impatrq/AVIS/Compras/Plantilla de Compras Completo/Gasto Total de SKYLF.pdf

# Gasto Total de SKYLF

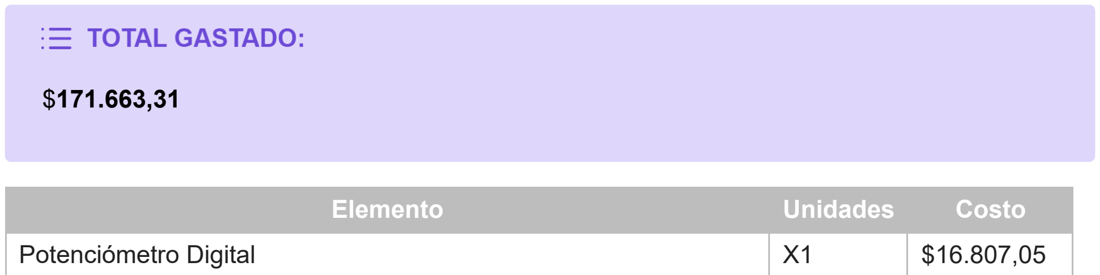
[picture p51: figure]
Elemento; Unidades; Costo; Potenciómetro Digital

Cables macho-macho | X1 | $4.900
MODULO ARDUINO CONVERSOR RS485 A TTL | X3 | $11.611,34
MODULO WIFI Y BLUETOOTH SERIE 32 BIT (30 PINES) | X1 | $23.795,07
ACELEROMETRO GIRÓSCOPO 6 EJES (MPU6050) | X1 | $3.090,90
PB20S HEMBRA 20 VIAS RECTO (Zócalos) | X2 | $1.435,06
PUL-ST030-N 15MM (Pulsadores) | X8 | $9.714,28
MECHA PARA METAL | X2 | $9.500
Disco de corte | X2 | $7.400
Tornillos | X17 | $1.700
Discos Flap | X2 | $10.400
Tuercas | X7 | $840
Arandelas | X10 | $1.100
Adaptador HDMI a VGA | X1 | $8.000
Optoacoplador | X8 | $11.200
Cables Macho-Macho 20cm Dupont | X40 | $4.500
Bulones | X11 | $3.550
Tuercas 1/4 | X6 | $320
Tuercas 1/2 | X3 | $600
1 Varilla Enroscada 100CM, 10 Tornillos, 10 Tuercas, 10 Arandelas | X1 | $4.000
WD-40 | X1 | $5.800
Disco Tyrolit Básico | X1 | $4.000
Cable HDMI | X1 | $6.500
Adaptador DisplayPort a HDMI | X1 | $9.500
Placa virgen 15cmx15cm | X1 | $4.100
Tornillos y Arandelas | X1 | $1.500
Llave Rotativa de 6 estados 1P6W | X1 | $3.260,37
TOTAL | | $169.124,07

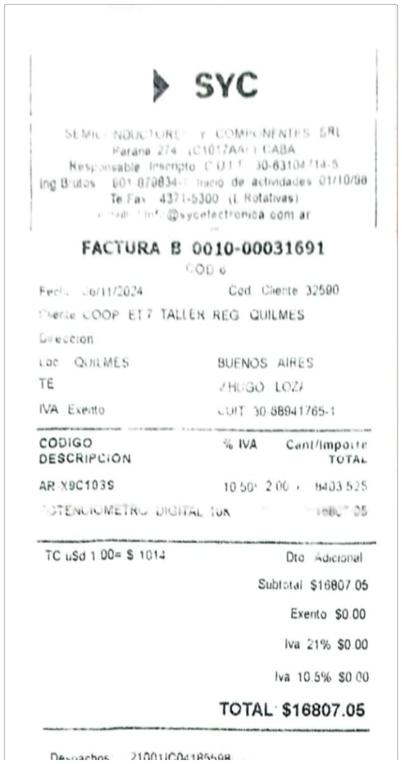
[picture p52: page 3]

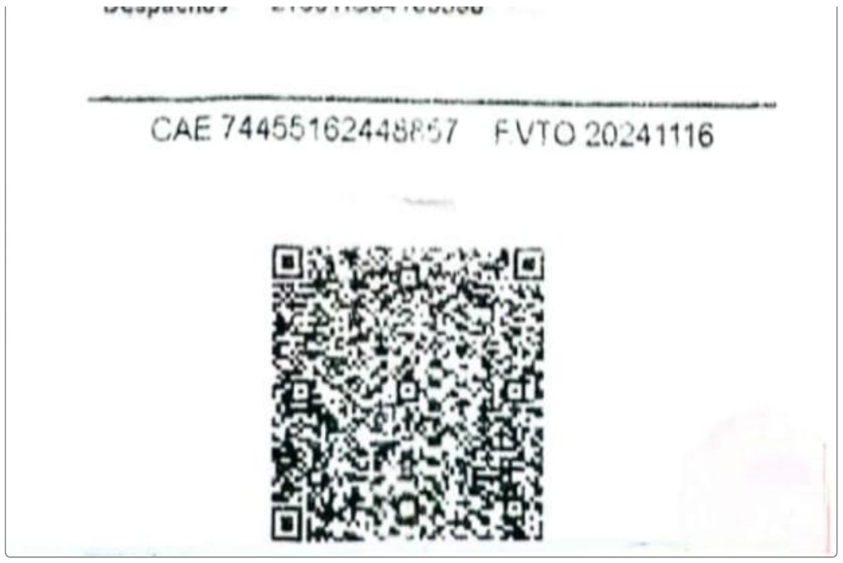
[picture p53: figure]
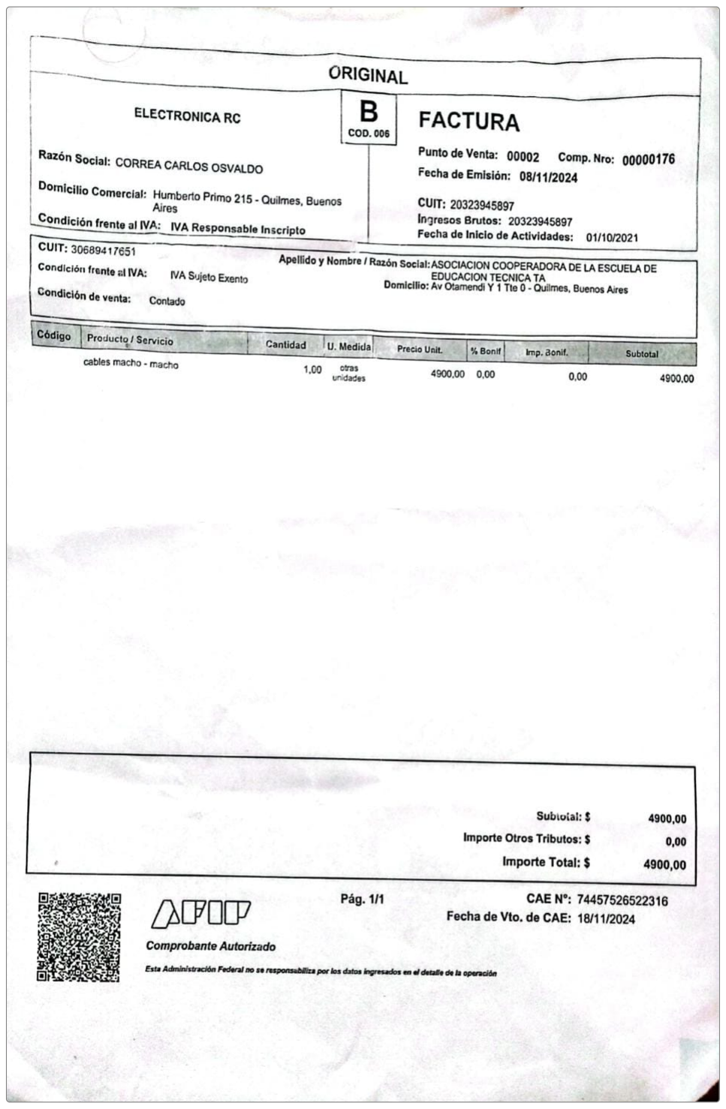
[picture p54: page 5]

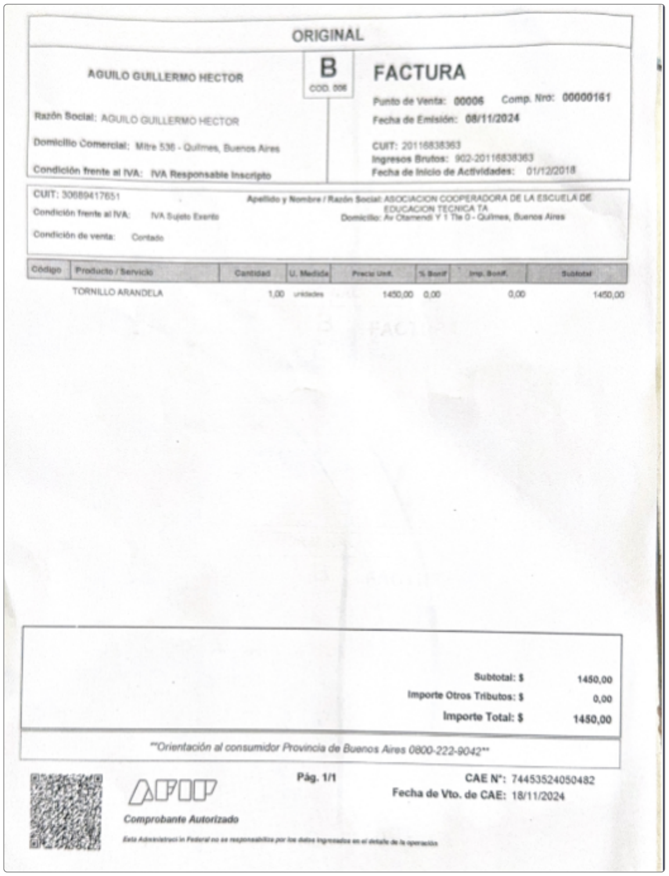
[picture p55: figure]
