impatrq/AVIS/Documentacion/Carpeta de campo y tecnica/Carpeta Técnica/Carpeta Tecnica SkylF .pdf

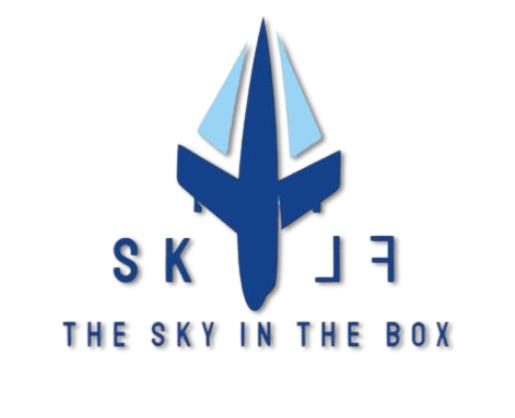
[picture p56: figure]

- Esteban Lautaro.
- Rubio Santiago Gabriel.
- Meabrio Lucas David.
- Flores Leandro.
- Brizuela Agustín.
- Leiva Santiago.
- Romocordoba Emiliano.
- Godoy Baldovino Jofiel

# S k y l F

# Integrantes

# Contacto

### Lautaro Esteban:

Mail: Lautyesteban14@gmail.com

Linkedin: Lautaro Sebastian Esteban (https://www.linkedin.com/in/lautaro-sebasti%C3%A1n-esteban-a5a8462a2)

Instagram: @lauty.esteban (https://www.instagram.com/lauty.esteban/profilecard/?igsh=MTU2dWFrOGU0dmdwdQ%3D%3D)

### Santiago Rubio:

Mail: Santy201205@gmail.com

Linkedin: Santiago Rubio (https://www.linkedin.com/in/santiago-rubio-a118932a8)

Instagram: @santy_201205 (https://www.instagram.com/santy_201205?igsh=MXU4d3c0bnNhZDNwZQ%3D%3D)

### Lucas Meabrio:

Mail: Meabriolucas@gmail.com

Linkedin: Lucas Meabrio (https://www.linkedin.com/in/lucas-meabrio-539666270/)

Instagram: @lucass_meab (https://www.instagram.com/lucass__meab?igsh=amc4NGF2cmF1d2J5)

### Leandro Flores:

Mail: leandro200flores@gmail.com

Linkedin: Leandro Flores (https://www.linkedin.com/in/leandro-flores-82538a2b0)

Instagram: @lean.floresss (https://www.instagram.com/lean.floresss?igsh=ZzdwNms0dDN3MDRu)

### Agustin Brizuela:

Mail: brizuu750@gmail.com

Linkedin: Agustin Lionel Brizuela (https://www.linkedin.com/in/agustin-lionel-brizuela-488690270)

Instagram: @agustiin.brizuela (https://www.instagram.com/agustiin.brizuela?igsh=MXFiYnRuNTdoem1uMg%3D%3D)

### Santiago Leiva:

Mail: Santiagoleiva745@gmail.com

Linkedin: Santiago Leiva (https://www.linkedin.com/in/santiago-leiva-3905942bb)

Instagram: @leivva.s (https://www.instagram.com/leivva.s?igsh=bDduN3BvdGFqMjRj)

### Emiliano Romocordoba:

Mail: Romoemiliano324@gmail.com

Linkedin:

Instagram:

### Jofiel Godoy Baldovino:

Mail: Markbaldj@gmail.com

Linkedin: Marco Baldovino (https://www.linkedin.com/in/marco-baldovino-b3948b2ba)

Instagram:@jofiel_godoy (https://www.instagram.com/jofiel_godoy?igsh=MXZpdGE5bm11NHJ5Nw%3D%3D)

# ÍNDICE

# Descripción del Proyecto:

# Variadores de Frecuencia:

Resumen del objetivo.

Lista de materiales usados.

# Paneles de Control:

# Descripción del Proyecto

Nuestro proyecto se enfocará en el armado y reacondicionamiento de un simulador de vuelo con el fin de recrear una experiencia inmersiva y entretenida para el que se meta dentro de la cabina.

# Variadores de Frecuencia

# Resumen del objetivo

El objetivo principal con el uso del variador de frecuencia es lograr una comunicación eficiente tanto con el programa de control como con los motores del simulador. Este tipo de comunicación es crucial para garantizar un funcionamiento sincronizado y preciso entre el software y el hardware. En nuestro caso, la comunicación se establece utilizando el protocolo Modbus, un estándar de comunicación ampliamente utilizado en sistemas industriales debido a su fiabilidad y flexibilidad.

El protocolo Modbus permite el intercambio de datos entre el variador de frecuencia y el microcontrolador ESP32, facilitando el control de parámetros clave como la velocidad y la dirección de los motores. Esta programación la estamos llevando a cabo mediante la plataforma Arduino IDE, donde se desarrollan los códigos que gestionan la interacción entre los distintos componentes del sistema. A través de Arduino IDE, se ha configurado el protocolo Modbus para que las señales enviadas desde el programa de simulación sean interpretadas correctamente por el variador de frecuencia, y a su vez, estas se traduzcan en comandos que controlan el movimiento de los motores.

# Lista de materiales usados

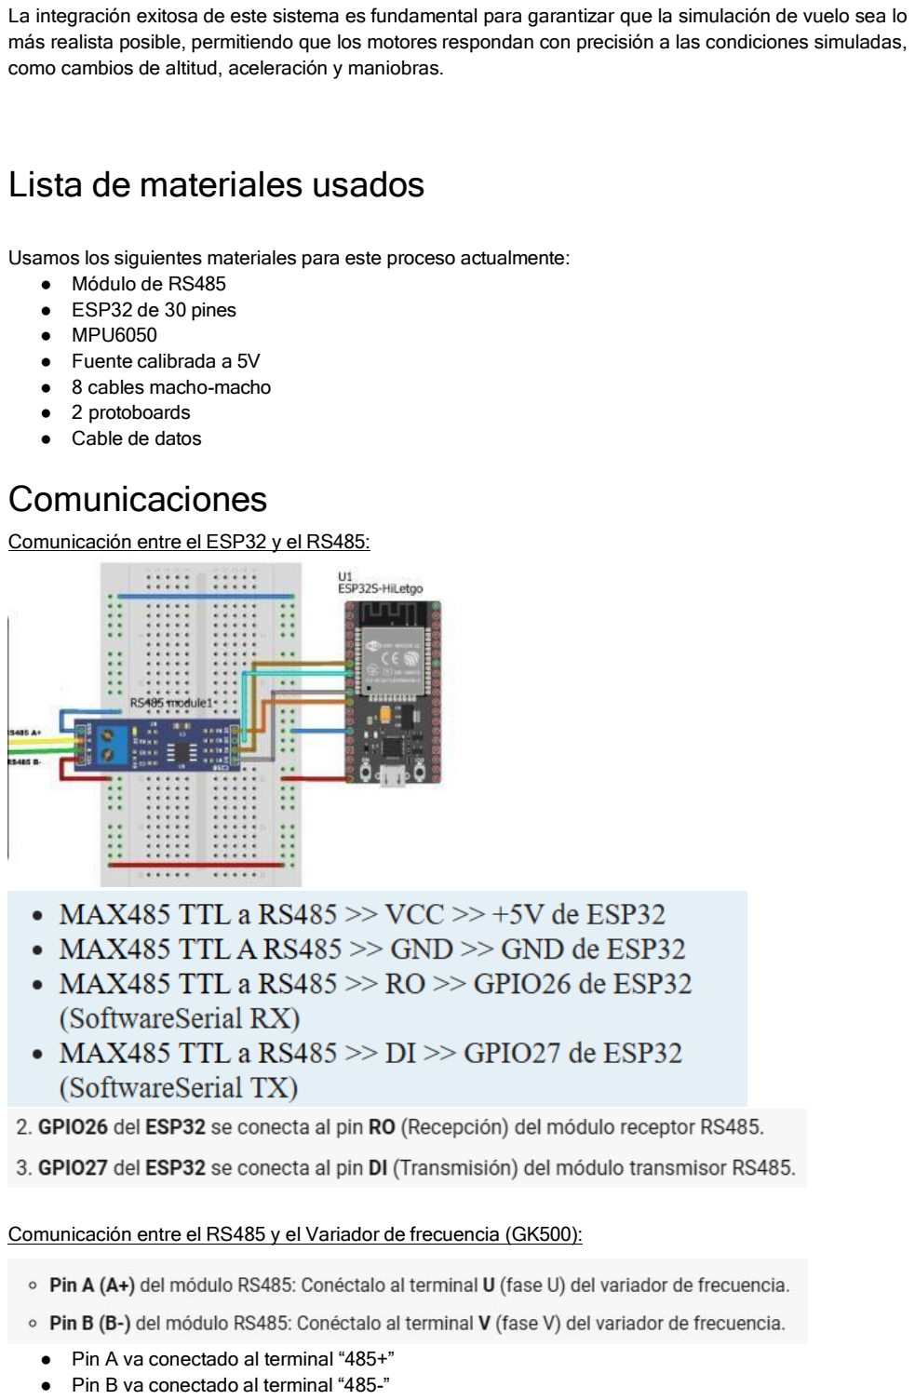
[picture p57: page 5]

La integración exitosa de este sistema es fundamental para garantizar que la simulación de vuelo sea lo más realista posible, permitiendo que los motores respondan con precisión a las condiciones simuladas, como cambios de altitud, aceleración y maniobras.

Usamos los siguientes materiales para este proceso actualmente:
- Módulo de RS485
- ESP32 de 30 pines
- MPU6050
- Fuente calibrada a 5V
- 8 cables macho-macho
- 2 protoboards
- Cable de datos

# Comunicaciones

Comunicación entre el ESP32 y el RS485:

Comunicación entre el RS485 y el Variador de frecuencia (GK500):

- Pin A va conectado al terminal “485+”
- Pin B va conectado al terminal “485-”

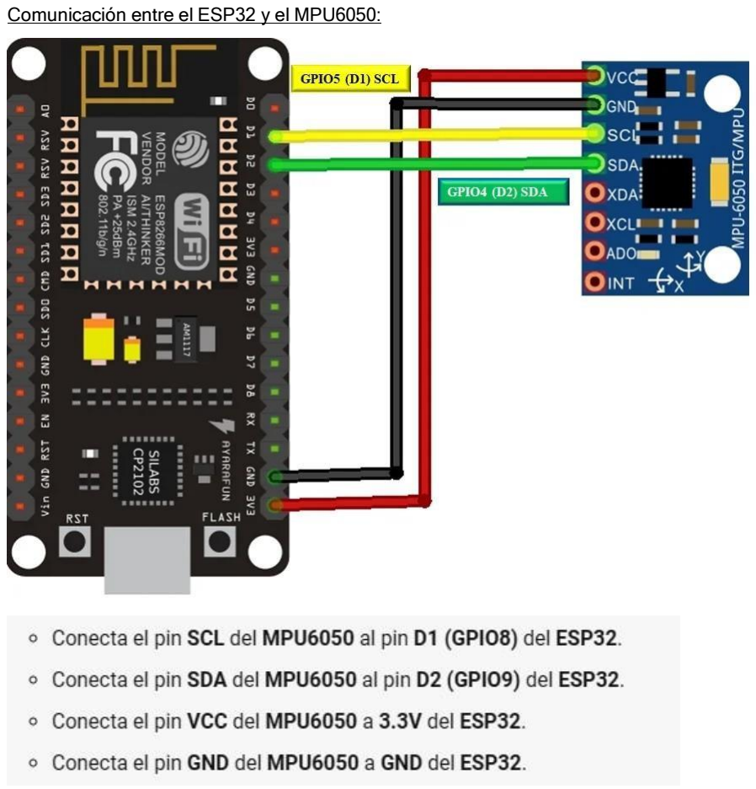
[picture p58: page 6]

Comunicación entre el ESP32 y el MPU6050:

# ESP32

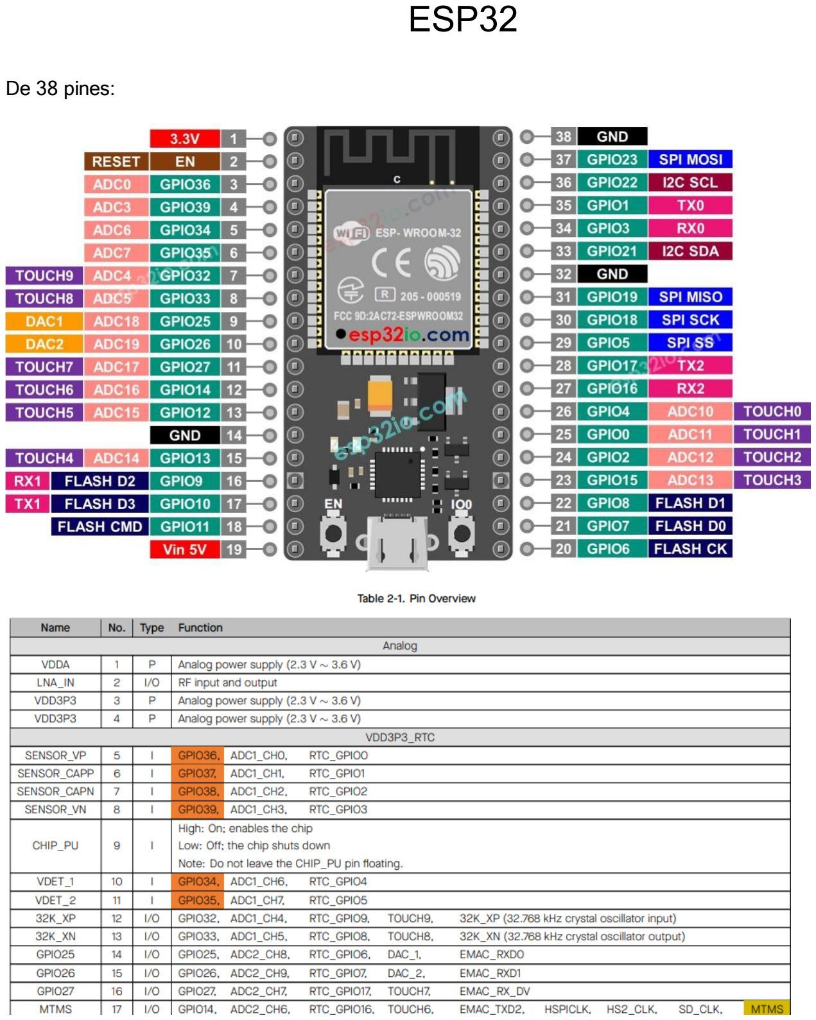
[picture p59: page 7]

De 38 pines:

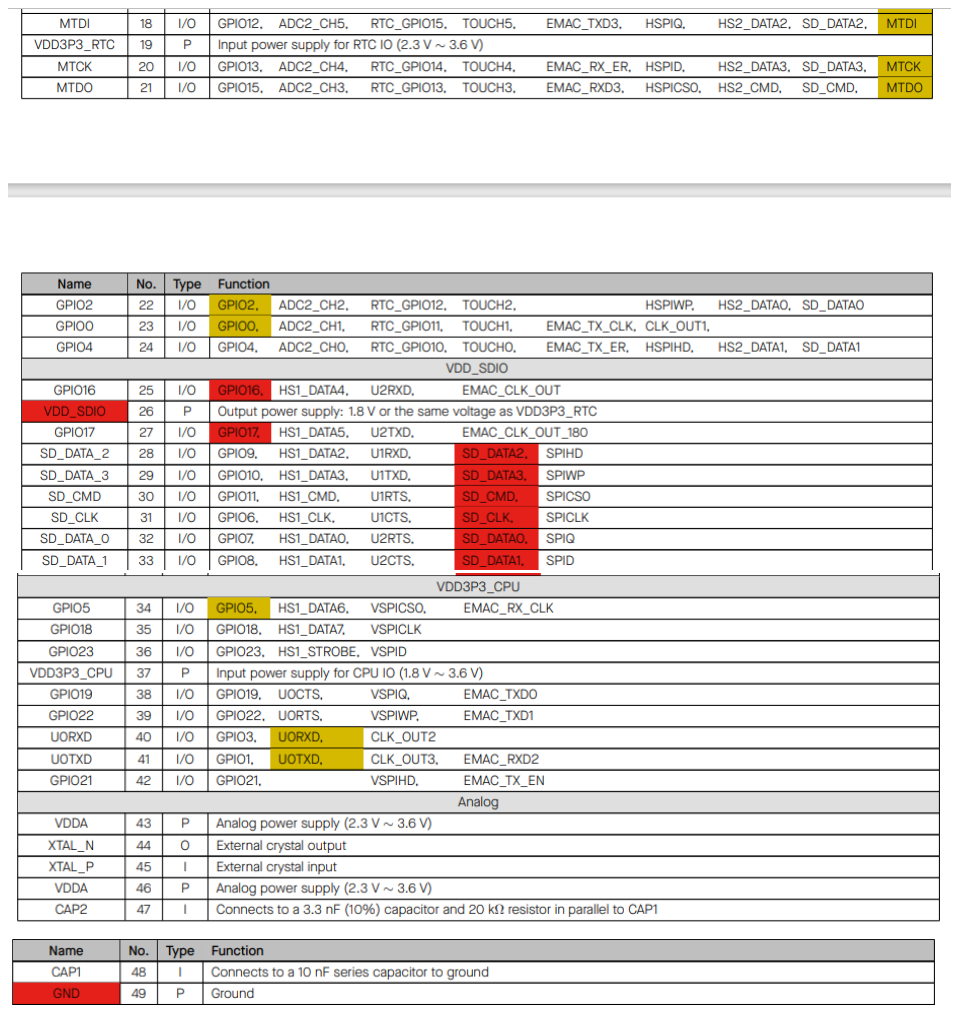
[picture p60: page 8]
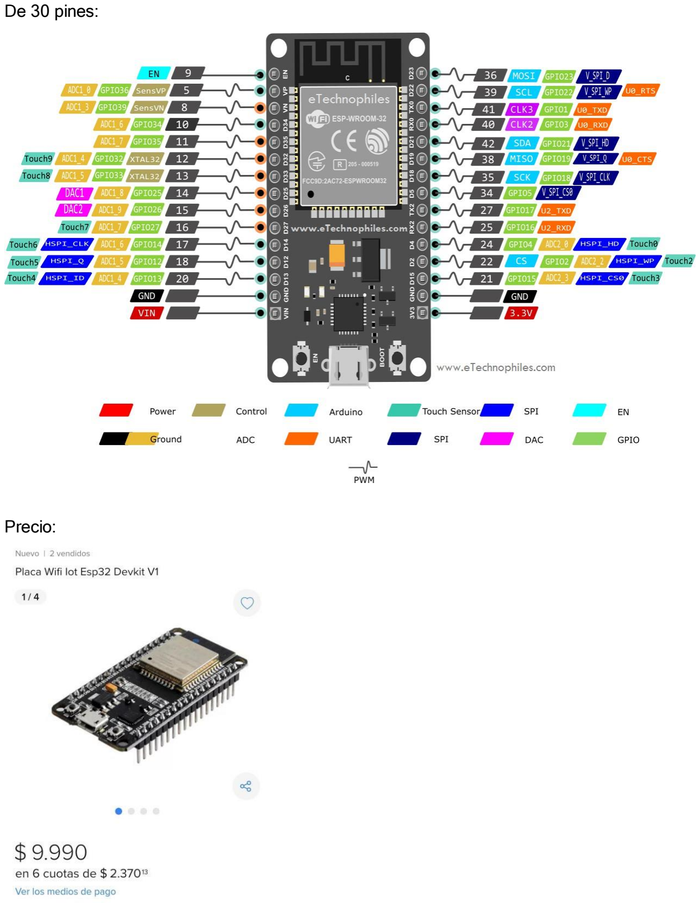
[picture p61: page 9]

De 30 pines:

Precio:

RS485

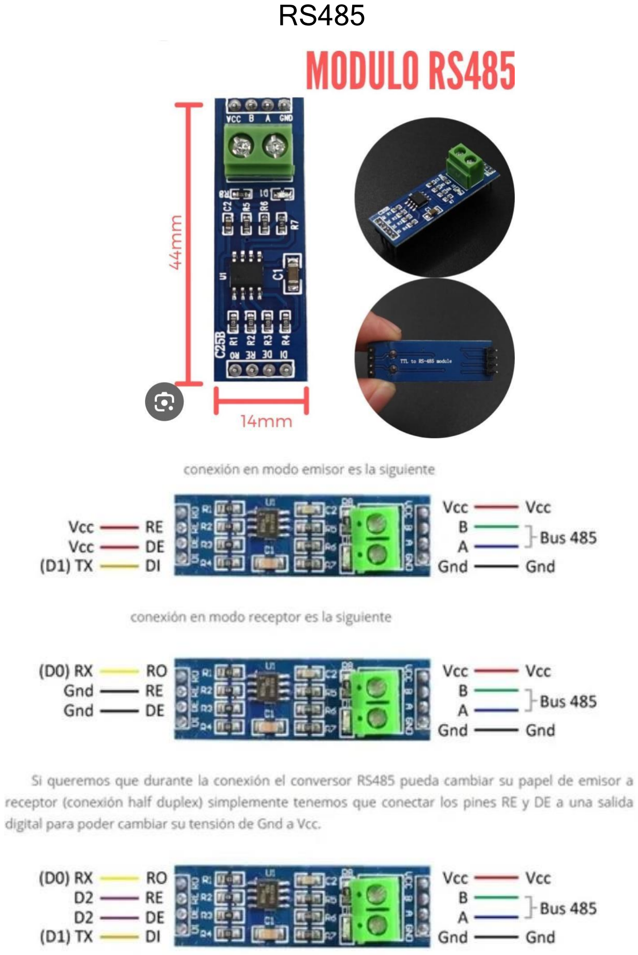
[picture p62: page 10]

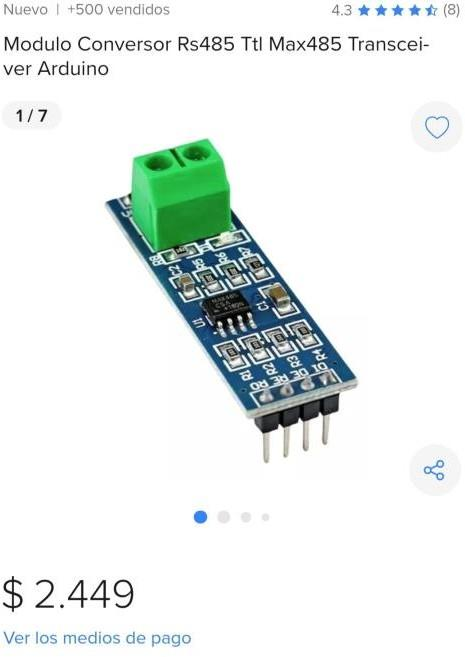
[picture p63: figure]

# MPU6050

El MPU6050 es una unidad de medición inercial o IMU (Inertial Measurment Units) de 6 grados de libertad, pues combina un acelerómetro de 3 ejes y un giroscopio de 3 ejes. Este sensor es muy utilizado en navegación, geometría, estabilización, etc. Este componente nos sirve para inclinar la cabina en sus 3 ejes, basándose en las mediciones de los SimVars.

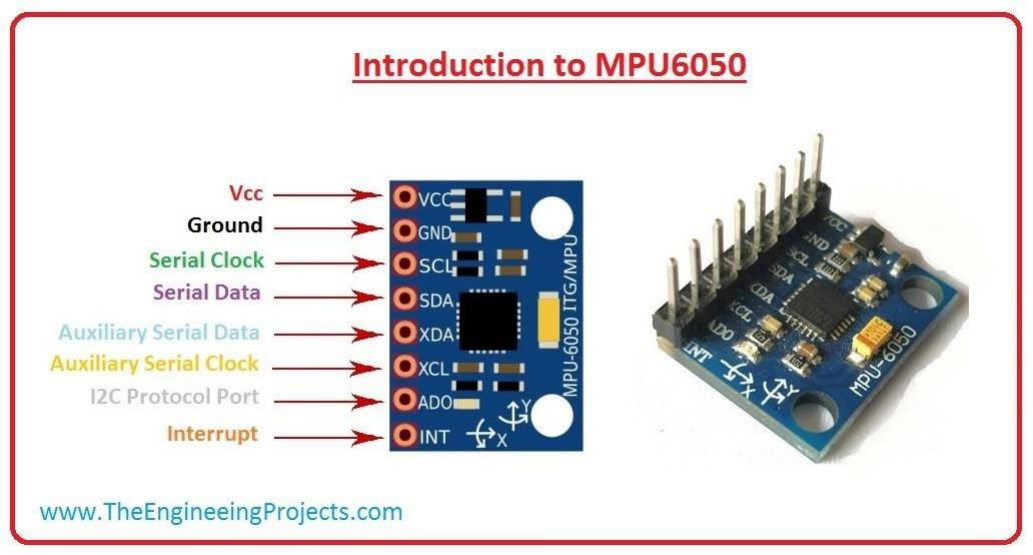
[picture p64: figure]

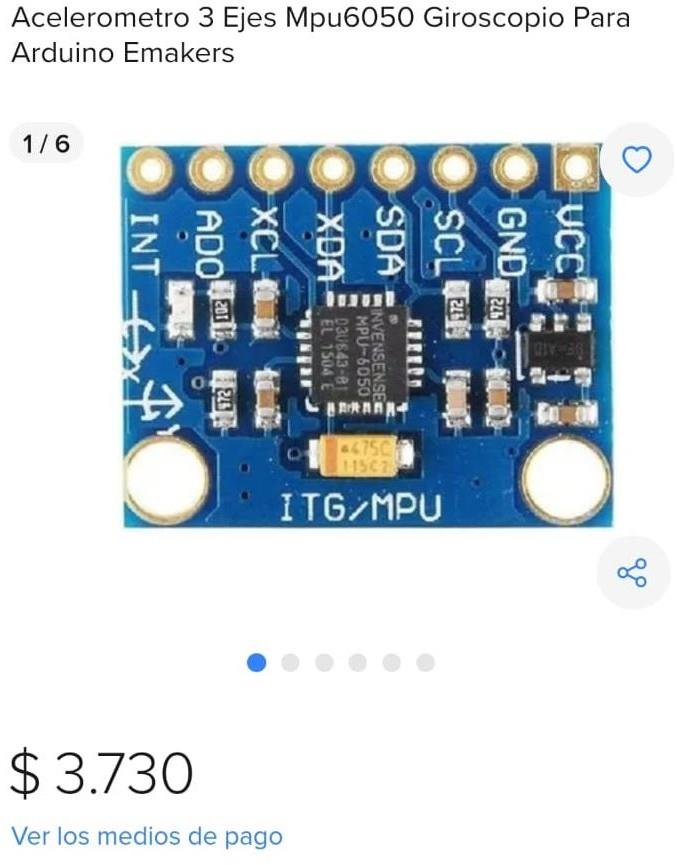
[picture p65: figure]

# Listado de parámetros que pusieron en el variador

Parámetros | Designación | Rango | Rango puesto
b0-01 | Fuente de Mando de Frecuencia Maestra | 0: Configuración Digital (b0-02) + ∧ /∨ Ajuste en Panel de Control 1: Configuración Digital (b0-02) + Ajuste por Bornera UP/DOWN 2: Entrada Analógica AI 3: Potenciómetro 6: Salida de PID 8: Comando Multivelocidad 9: Comunicación

9

9: Comunicación

b0-02 | Configuración Digital de Frecuencia Maestra | Límite Inferior ~ Límite Superior de Frecuencia

50,00 Hz

b1-00 | Comando RUN | 0: Control por Panel de Control 1: Control por Bornera 2: Control por Comunicación

2

2: Control por Comunicación

b1-01 | Enlace de comando run y configuración frecuencia | Unidades: Fuente de configuración frecuencia agrupada bajo control panel de control: 0: Sin enlace 1: Configuración Digital (b0-02) + ∧ /∨ Ajuste en Panel de Control 2: Configuración Digital (b0-02) + Ajuste por Bornera UP/DOWN 3: AI 4: Potenciómetro 7: Salida de PID 9: Comando Multivelocidad A: Entrada de Comunicación Decenas: Fuente de

AAA

A: Entrada de Comunicación

Parámetros | Designación | Rango | Rango puesto
| | configuración frecuencia agrupada bajo control terminal (igual a unidades) Centenas: Fuente de configuración frecuencia agrupada bajo control de comunicación (igual a unidades)
H0-01 | Configuración del Puerto de Comunicación RS-485 | Unidades: Velocidad en Baudios 0: 4800 bps 1: 9600 bps 2: 19200 bps 3: 38400 bps 4: 57600 bps Decenas: Formato de datos 0: Formato 1-8-2-N, RTU 1: Formato 1-8-1-E, RTU 2: Formato 1-8-1-O, RTU 3: Formato 1-7-2-N, ASCII 4: Formato 1-7-1-E, ASCII 5: Formato 1-7-1-O, ASCII Centenas: Tipo de conexión 0: Conexión cable directo (232/485) 1: MODEM (232) Unidades de Mil: Almacenamiento 0: Sin almacenar ante Pérdida de Energía 1: Almacenado ante Pérdida de Energía

0001

1: 9600bps

H0-05 | Opción Maestro/Esclavo

0: Se usa independientemente 1: Como Maestro
2: Como Esclavo

2

2: Como Esclavo

# Paneles de Control

El simulador posee dos paneles que cumplen su respectiva función; el panel de control (mediante palancas y botones interactuando con el entorno virtual) y el panel de instrumentos (estos se van a mostrar mediante una tele que transmite los datos reales de vuelo en los instrumentos)
El panel de control cuenta con todo el Hardware que se comunicará con el software a utilizar, (que en nuestro caso sería el Flight Simulator 2020).

## Panel de Control

En el panel de control hay 7 interruptores de palanca, una llave selectora rotativa de 6 estados y una llave con dos interruptores.
Para que estos componentes se accionen en simultáneo al vuelo que se haga en el Flight Simulator 2020, a través de una herramienta llamada "MobiFlight" y un Arduino UNO. Con el MobiFlight asignamos a cada componente a que realice determinada acción dentro del FS2020. Y con la Arduino UNO, en conjunto al MobiFlight, ejecuta esa acción a realizar
A continuación, explicaremos cuáles son estos componentes a utilizar y cuál es su función dentro del entorno virtual del FS2020:

Interruptores de palanca:

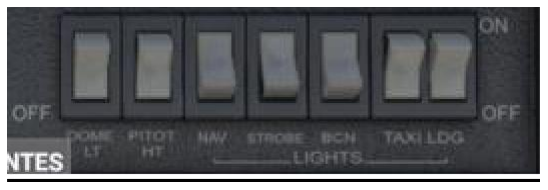
[picture p66: figure]

- 7 teclas de navegación:
- Tecla 1 “Dóme LT”: Cóntróla las luces interióres del avió´n.Se usa para iluminar la cabina durante el vueló nócturnó ó en cóndiciónes de póca luz.
- Tecla 2 “Pitót Hit”: Activa el sistema de calefacció´n del tubó Pitót.
- Tecla 3 “Nav”: Enciende las luces de navegació´n, que són las luces de pósició´n en las alas y la cóla.
- Tecla 4 “Stróbe”: Activa las luces estróbóscó´ picas, són luces blancas intermitentes en las alas.
- Tecla 5 “BCN”: Enciende la Luz de baliza (beacón), una luz rója intermitente ubicada en la parte superiór ó inferiór del fuselaje. Si el mótór este encendidó, esta luz siempre se encendera´.

- Tecla 6 “Taxi”: Enciende la luz de taxi, es una luz delantera usada para iluminar la pista mientras el avió´ n rueda pór el sueló.
- Tecla 7 “LDG”: Cóntróla la luz de aterrizaje, usada para iluminar la pista durante el aterrizaje ó despegue.
- Primer: se encarga de inyectar cómbustible a lós cilindrós del mótór antes de arrancarló, facilitandó el arranque en cóndiciónes especialmente frias. (Generalmente se bómbea 2 a 3 veces).
- Llaves:
- Llave maestra ALT: esta se encarga de encender el alternadór del mótór para póder cargar la baterí´a de la aerónave.
- Llave maestra Bat On/Off: esta se encarga de prender la baterí´a para que pueda alimentar lós circuitós ele´ctricós de la aerónave.

Magneto (con llave selectora rotativa de 6 estados):

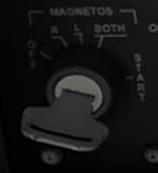
[picture p67: figure]

- Magnetó: este cuenta cón 5 estadós:
- Estadó 1 “OFF”: Ambós magnetós esta´n apagadós, y el mótór nó recibira´ chispa.
- Estadó 2 “Right”:Sóló el magnetó derechó estara´ encendidó.
- Estadó 3 “Left”:Sóló el magnetó Izquierdó estara´ encendidó.
- Estadó 4 “Bóth”: Ambós magnetós esta´n activós (pósició´n nórmal durante el vueló)
- Estadó 5 “Start”: Esta pósició´n activa el mótór de arranque y ambós magnetós, usada sóló para el encendidó del mótór

## Instrucciones de Configuración

Vinculación del MobiFlight con el FS2020 y el Arduino UNO

Para que el MobiFlight se vincule con el hardware del simulador de vuelo, nos tiene que aparecer en la barra inferior una tilde que confirme si se vincularon los siguientes parámetros:

Module:
- Si no hay ningún microcontrolador conectado al MobiFlight aparecerá un triangulo amarillo indicando eso

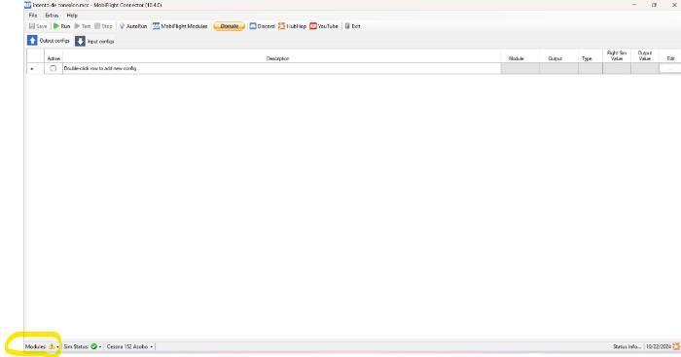
[picture p68: figure]

- Caso contrario, si está conectado al MobiFlight algún Microprocesador, (siendo el Arduino UNO en nuestro caso) se indicará que MobiFlight lo detectó correctamente.

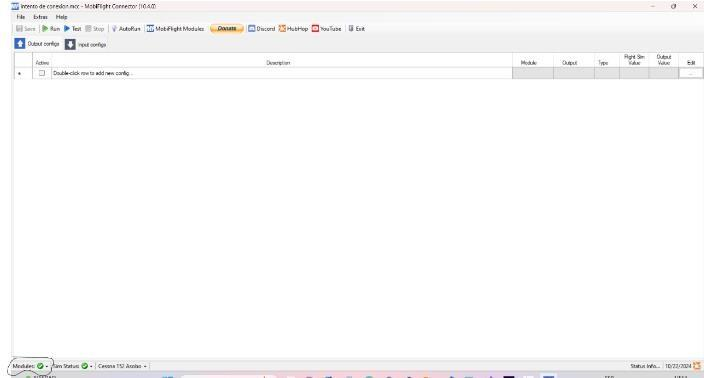
[picture p69: figure]

Sim Status
- El Sim Status indica el estado de las conexiones al simulador de vuelo
En nuestro caso usamos el programa "FSUIPC7" para que el FS2020 detecte el hardware. Así nos tiene que aparecer:

Configuración de las Palancas en el MobiFlight

Paso a Paso de configuración de palancas para vincularlas con MobiFlight y el FS2020

### 1. Conectamos elArduino UNOal MobiFlight y elFSUIPC7

### 2. Asignamos unPindel2 al13 delArduinoUNOa uno de los terminales de la palanca (En nuestro caso lo pusimos al pin 8 pero puede ser cualquiera)

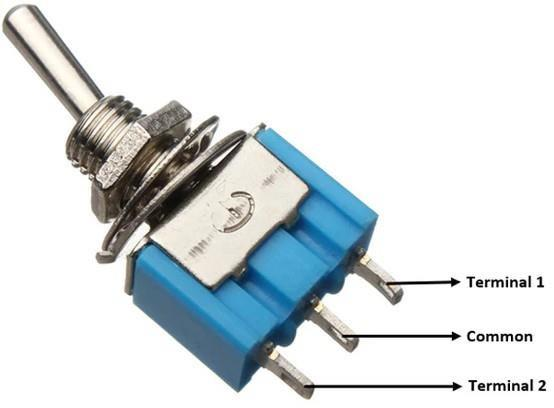
[picture p70: figure]

### 3. Seleccionar enMobiFlightla pestaña de "MobiFlight Modules"

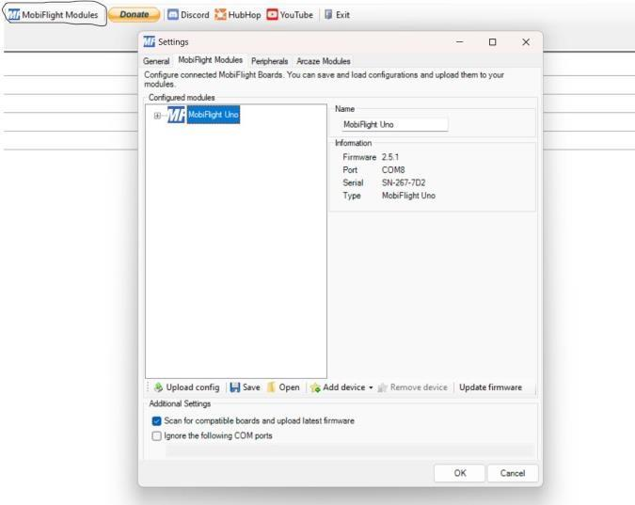
[picture p71: figure]

### 4. Para no tener inconvenientes actualizar el firmware así el MobiFlight detecte correctamente el la Arduino UNO

### 5. Enla barra inferior ir a la pestaña de "AddDevice" para agregar undispositivo que en

nuestro caso es una Palanca.

### 6. Luegoleasignamos ala palanca el nombrecon el que queramos quese identifique, siendo en

este caso "Tubo Pitot" para la función de la palanca que es sobre el Calentador del Tubo Pitot

### 7. Poner enla "Configuraciónde Pin" elpinque le asignamos a la palanca (ennuestro caso el Pin 8 de la Arduino UNO)

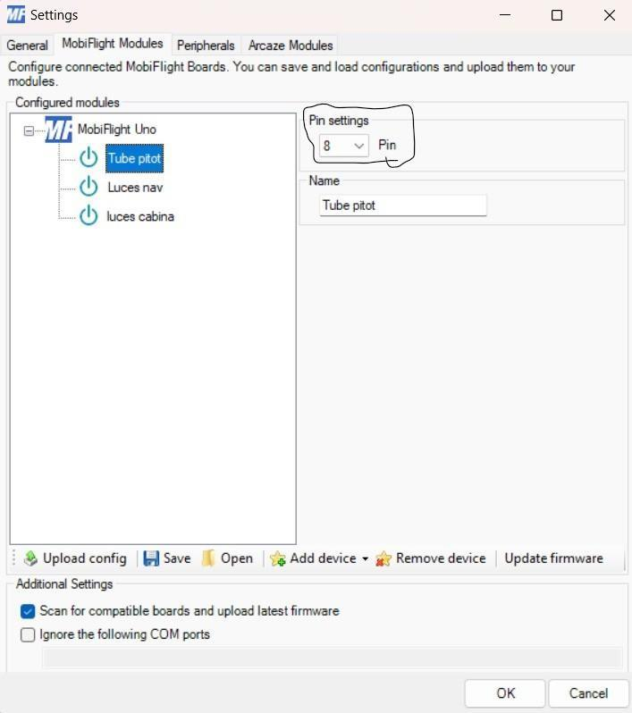
[picture p72: figure]

### 8. Enel Menú principal crear una configuraciónde entrada en el "InputConfigs"

### 9. Para editar la configuraciónselecciona a la derecha de la fila en"Edit"

### 10. Luego seleccionar los dispositivos conectados alMobiFlight

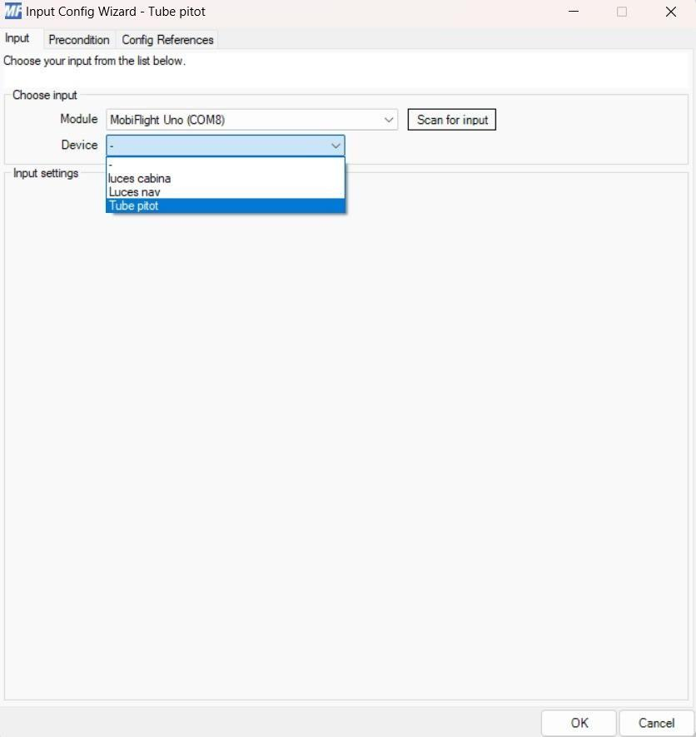
[picture p73: figure]

### 11. Seleccionar enelActionType el "FSUIPC - Offset"para luego asignarle la acciónal dispositivo que hayamos conectado (en nuestro caso la palanca)

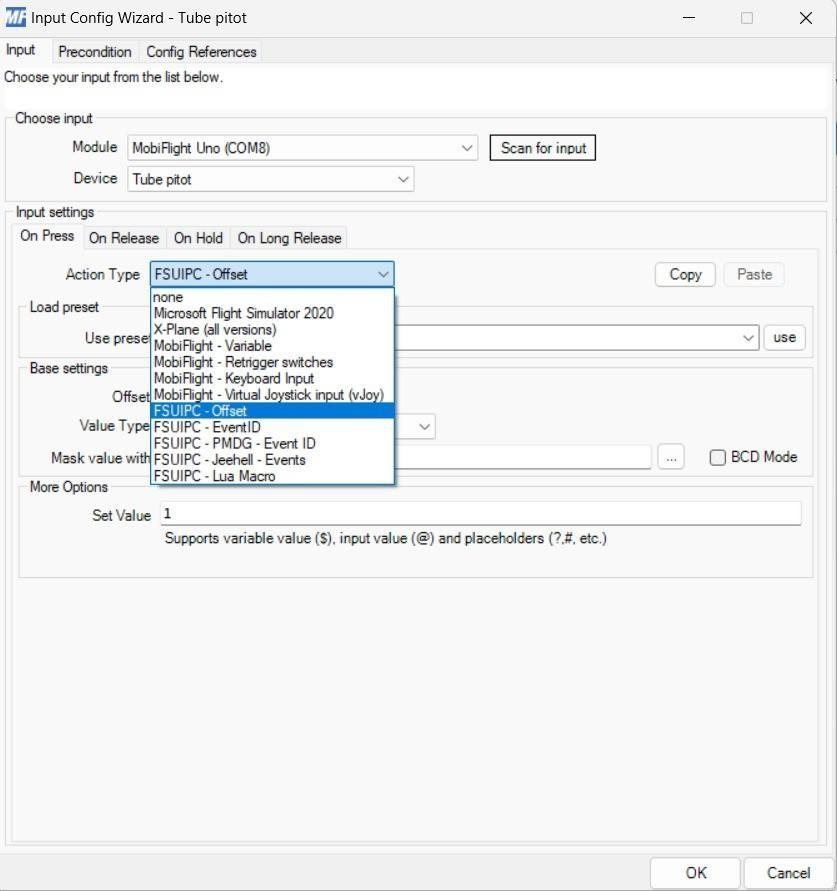
[picture p74: figure]

### 12. Dentro de la configuración de entrada se encuentran las configuraciones para cuando se activa la palanca "OnPress" y cuando está del lado contrario "OnRelease"

13. Para la configuración del Offset nos fijamos en el manual de Offset del FSUIPC que está

### eninternet para buscar la acción de la palanca, y nos dice cuál código deOffsettiene que

ir.

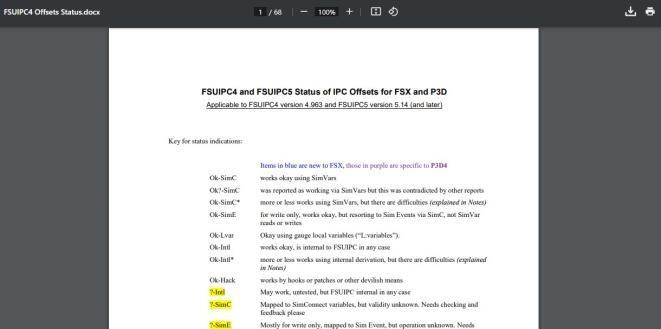
[picture p75: figure]

### 14. Ennuestro casobuscamos eldel calentadordeltubo pitot.Por lo que ponemos el que nos dice "029C"

### 15. Paraque elCalentador deltubo pitotdelCessna 152se active ensimultáneo a la

palanca que conectamos al FS2020, le asignamos "1" como valor de seteo.

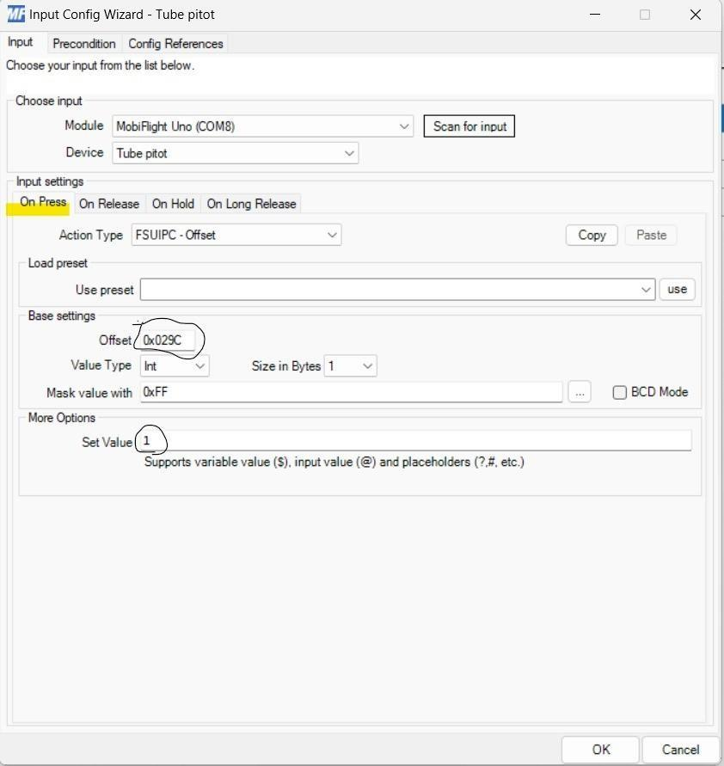
[picture p76: figure]

### 16. En"OnRelease" de igualforma poner el mismo código deOffet peroque cuando se baje la palanca que el calentador se apague ponemos "0" como valor de seteo

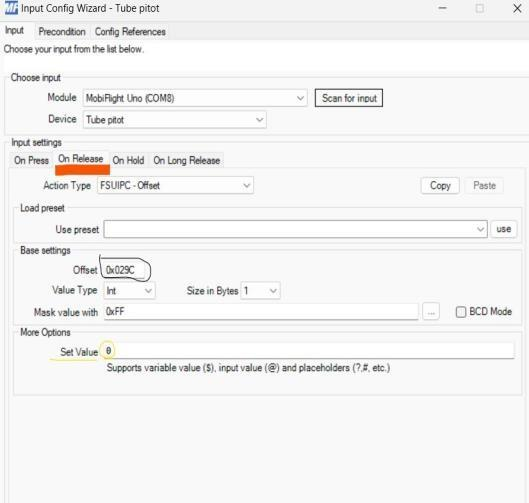
[picture p77: figure]

### 17) Luego de esto al probar la palanca que vinculamos a dispositivo que sea (en nuestro caso el calentador deltubo pitot), se tendr

Estructura:
Estos componentes irán colocados en una madera rígida pero liviana, la cuál ha sido medido con el fin de mejorar la estética, y esta medida sería de 500mmx140/120mm. Ya cortadas las medidas se colocarán los interruptores y demás componentes. Luego en la parte final se pintará la madera con un aerosol negro y se pondrán letras en blanco que formen los nombres de cada interruptor, tal como en una cabina real del CESSNA 172 para dar más realismo.

## Panel de Visualización de Instrumentos

Con el fin de generar una experiencia realista de vuelo, implementamos un Panel de Instrumentos virtual, el cuál por medio de una pantalla de 17 pulgadas transmitiremos los datos reales de cada instrumento de vuelo. Por lo que para transmitir esos datos o también llamados “Variables”, se encargan los programadores del equipo: Santiago Rubio y Lucas Meabrio.
Para darle una mejor estética al panel de instrumentos y que no sea solo una televisión mostrando los instrumentos, decidimos usar una placa de plástico con los agujeros de los instrumentos del avión usada por el grupo anterior del simulador (AVIS), la cuál para la fecha de la exposición será forrada para mejorar la estética del panel en conjunto a el otro panel.
Una parte importante del Panel de Instrumentos es toda la labor de Personalización de la ubicación de los instrumentos en la pantalla. Nosotros elegimos usar una aplicación creada por la comunidad de FS2020 llamada “Pop Out Panel Manager”, para así que se muestre de la forma que queramos en la pantalla de 17 pulgadas los instrumentos de vuelo.

## MATERIALES:

- 1 Madera para el panel de control
- 1 Placa de plástico con los agujeros para cada instrumento
- 2 Arduino UNO
- 40 cables macho-macho aprox.
- 1 llave selectora rotativa de 6 estados
- 7 interruptores de palanca
- 8 pulsadores – PUL-ST030-N
- 4 interruptores/switches
- 1 Televisión de 18 pulgadas
- 1 Aerosol de color negro/balde de pintura color negro
- 1 Pack de letras transferibles color blanco
- 2 SIMPLE FILA CONTACTO DOBLE PASO – PB20S

## GASTOS:

- Potenciómetro Digital
Unidades: X1
Costo: $16.807,05
- Cables macho-macho
Unidades: X1
Costo: $4.900
- Módulo Arduino Conversor RS485 a TTL Unidades: X3
Costo: $11.611,34
- Módulo WiFi y Bluetooth Serie 32 Bit (30 Pines) Unidades: X1
Costo: $23.795,07
- Bornera Triple Azul para Impreso 8A 300V Unidades: X5
Costo: $2.679,63
- Acelerómetro Giróscopo 6 Ejes (MPU6050) Unidades: X1
Costo: $3.090,90
- PB20S Hembra 20 Vías Recto (Zócalos) Unidades: X2
Costo: $1.435,06
- PUL-ST030-N 15MM (Pulsadores) Unidades: X8
Costo: $9.714,28
- Mecha para Metal
Unidades: X2
Costo: $9.500
- Disco de Corte
Unidades: X2
Costo: $7.400
- Tornillos
Unidades: X17
Costo: $1.700

- Discos Flap
Unidades: X2
Costo: $10.400
- Tuercas
Unidades: X7
Costo: $840
- Arandelas
Unidades: X10
Costo: $1.100
- Adaptador HDMI a VGA
Unidades: X1
Costo: $8.000
- Optoacoplador
Unidades: X8
Costo: $11.200
- Cables Macho-Macho 20cm Dupont Unidades: X40
Costo: $4.500
- Bulones
Unidades: X11
Costo: $3.550
- Tuercas 1/4
Unidades: X6
Costo: $320
- Tuercas 1/2
Unidades: X3
Costo: $600
- 1 Varilla Enroscada 100CM, 10 Tornillos, 10 Tuercas, 10 Arandelas Unidades: X1
Costo: $4.000
- WD-40
Unidades: X1
Costo: $5.800
- Disco Tyrolit Básico
Unidades: X1
Costo: $4.000
- Cable HDMI
Unidades: X1
Costo: $6.500
- Adaptador DisplayPort a HDMI Unidades: X1
Costo: $9.500
- Placa Virgen 15cmx15cm
Unidades: X1
Costo: $4.100
- Tornillos y Arandelas
Unidades: X1
Costo: $1.500
- Llave Rotativa de 6 Estados 1P6W Unidades: X1
Costo: $3.260,37

## GASTO TOTAL: $171.803,7
