impatrq/AVIS/Microsoft Flight Simulator/Movimientos del avion/Variables movimientos y controles/SimVars de movimiento del avion.pdf

# Variables de simulación (Simvars)

Los simvars permiten obtener el estado de un componente en la simulación (por ejemplo, el heading), ya sea recopilarlos para mandarselos a un micro o para ser modificados (depende del simvar, algunos no se pueden configurar) y se accede a ellas usando el formato RPN:
" (A:[simvar_name]:[simvar_index], [units]) "
simvar_name = nombre de la variable
simvar_index = el índice del circuito (muy pocos simvars lo requieren)
units = La unidad en la que está representada la variable (booleano, entero, etc)

A veces los simvars requieren de 2 índices, el índice del circuito y el índice del bus:
" (>A:BUS LOOKUP INDEX, Number) (A:CIRCUIT CONNECTION ON:45, Bool) " Number = Ahí va el índice del bus
Otra forma:
" (A:1:CIRCUIT CONNECTION ON:45, Bool) "
1 = índice del bus / 45 = índice del circuito

Hay que tener en cuenta que varias variables son escritas con "snake case" y con el prefijo, ya que así es como aparecen en el propio código de simulación:
" SIMVAR_CIRCUIT_ON -> (A:CIRCUIT ON:1, Bool) "

## Variables que podemos necesitar:

1) Para poder realizar los movimientos del avión:
a) Yaw (guiñada):

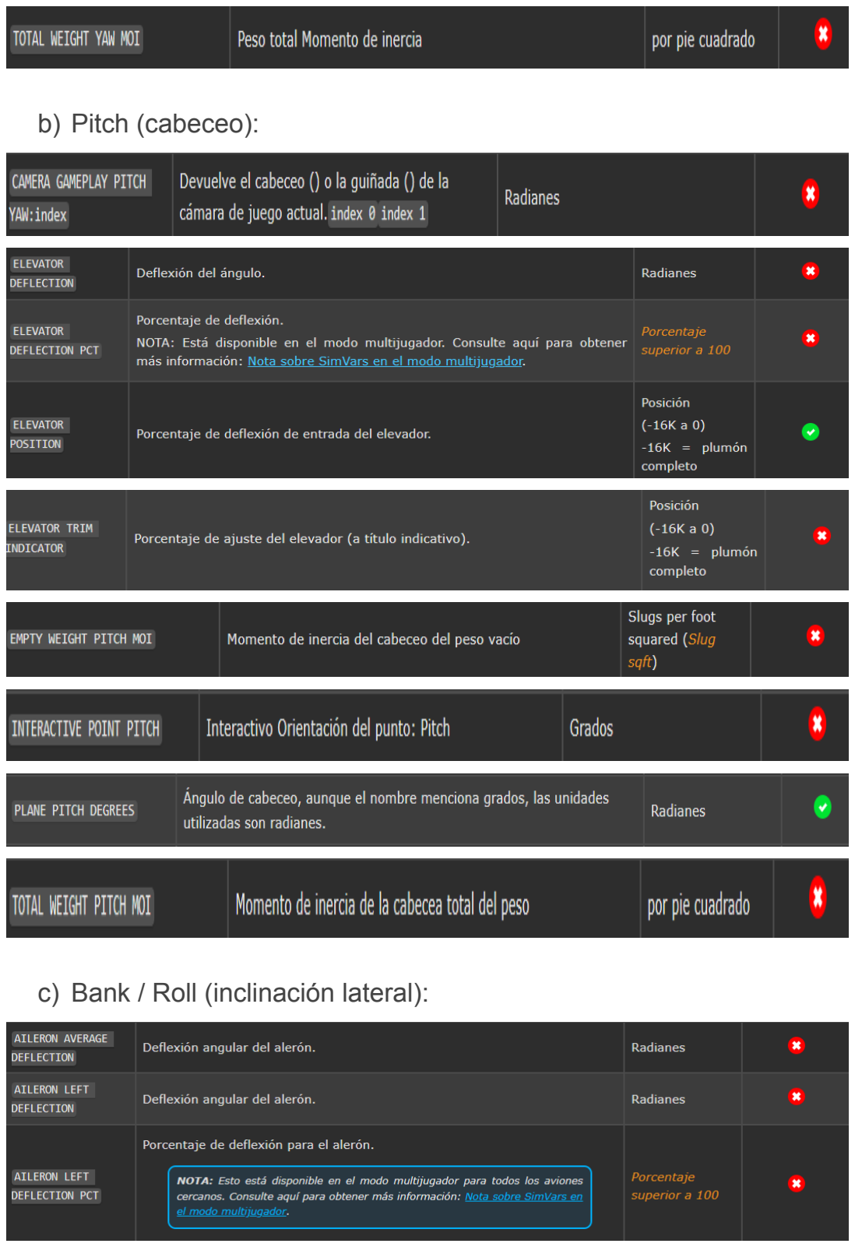
[picture p79: page 2]

b) Pitch (cabeceo):
c) Bank / Roll (inclinación lateral):

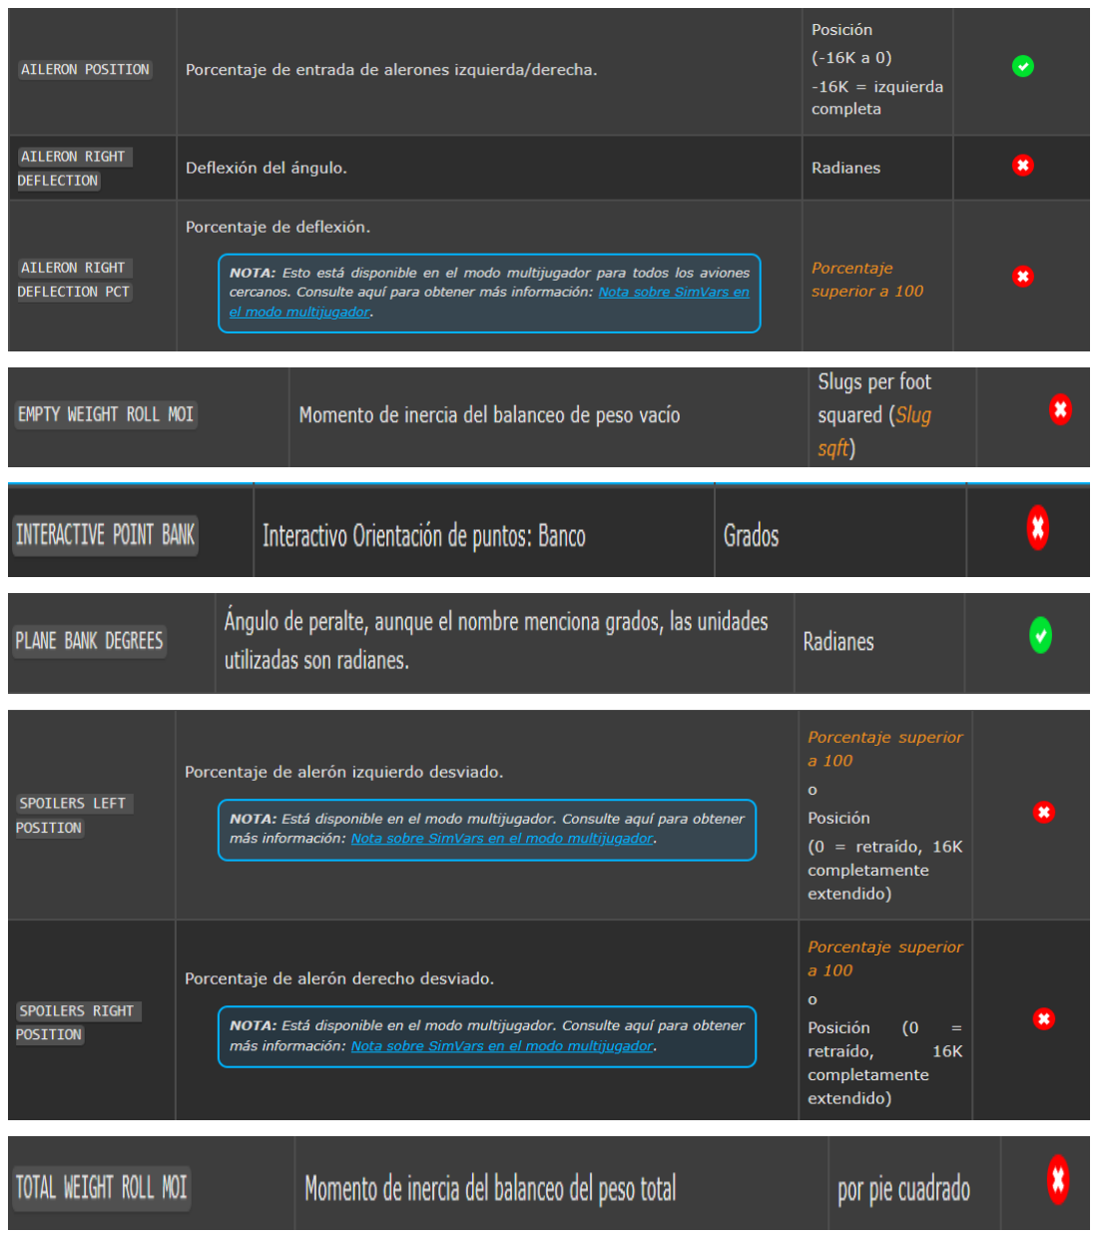
[picture p80: page 3]
