impatrq/AVIS/Documentacion/Carpeta de campo y tecnica/Carpeta de Campo/Julio.pdf

2/7
El grupo busco en conjunto soluciones para el variador de frecuencia y cómo hacerlo funcionar.
Empezamos investigar sobre la comunicación del variador de frecuencia con la computadora a través de LabVIEW y realizar pruebas por esa aplicación mandando instrucciones básicas al variador de frecuencias.
9/7
probamos el Rs485 que nos dió el profesor Medina (en las vacaciones nos dimos cuenta que no funcionó)
Se empezo a actualizar el panel de instrumentos de la cabina
Se revisó el presupuesto del simulador .generamos contenido para redes, y intentamos desarrollar alguna mejora para el panel (buscar material para forrarlo, diseñar alguna manera para reducir algún impacto hacia el panel) ----------------------------------------------------
VACACIONES DE INVIERNO
