impatrq/AVIS/Documentacion/Carpeta de campo y tecnica/Carpeta de Campo/Mayo.pdf

C.c Mayo
14/5/24
.Lautaro Esteban, Agustín Brizuela y Lucas Meabrio repasaron lo más importante a mencionarse en la entrevista que se daría el día siguiente en la radio “Radio Coctel Max”. 15/5/24
-Esteban, Godoy, Meabrio y brizuela tuvieron la entrevista en la radio Coctel Max

.Santiago Rubio estuvo realizando el croquis de la cabina

Santiago Leiva y Agustín Brizuela tomaron las mediciones de la cabina para que Santiago Rubio pueda hacer el croquis
21/5/24
.No se hizo ninguna actividad relacionada con el proyecto. Esto es porque estudiamos para una prueba que teníamos esta tarde con el profe Salinas.
28/5/24
.Esteban y Meabrio hicieron la lista de componentes subida en el drive que nos pasó Medina.
.Brizuela analizo empresas para intentar conseguir un patrocinio o sponsor que logre favorecer al grupo Skyfly y al simulador de vuelo
