impatrq/AVIS/Documentacion/Carpeta de campo y tecnica/Carpeta de Campo/C.c julio.pdf

C.c Julio

2/7
El grupo busco en conjunto soluciones para el variador de frecuencia y como hacerlo funcionar

9/7
Lautaro Esteban, Santiago Rubio, Santiago Leiva y Leandro Flores probaron el Rs485 que nos dió el profesor Medina (en las vacaciones nos dimos cuenta que no funcionó) Agustín Brizuela, Jofiel Godoy y Lucas Meabrio empezaron a actualizar el panel de instrumentos de la cabina
Emiliano Romo Córdoba y Santiago Leiva contribuyeron con las redes sociales y la búsqueda de sponsors para el proyecto
VACACIONES DE INVIERNO
