impatrq/AVIS/Estructura/4ef9c60f-1755-43bd-bb3c-9a162623d09b.jpg

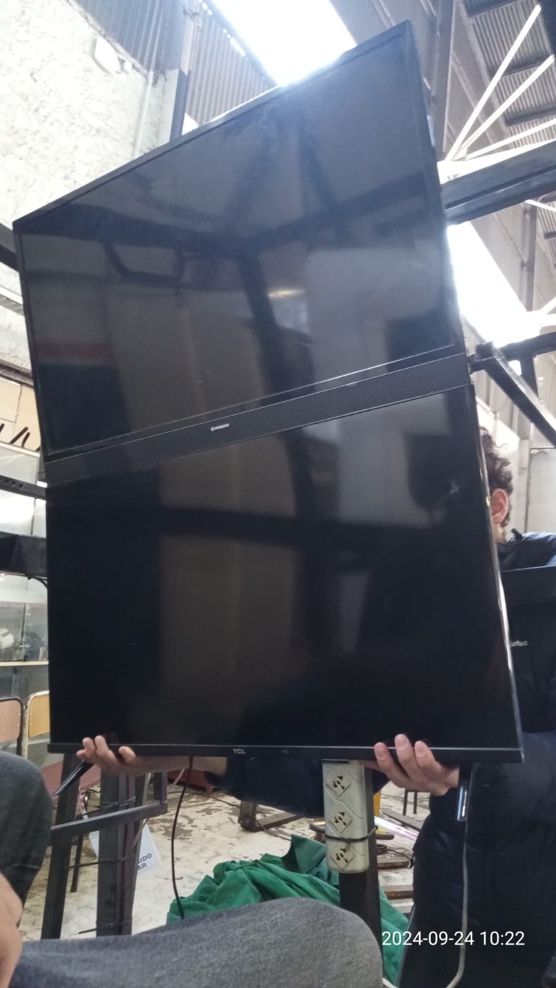
Estructura/4ef9c60f-1755-43bd-bb3c-9a162623d09b.jpg
