impatrq/AVIS/Estructura/cortando la estructura para panel.jpg

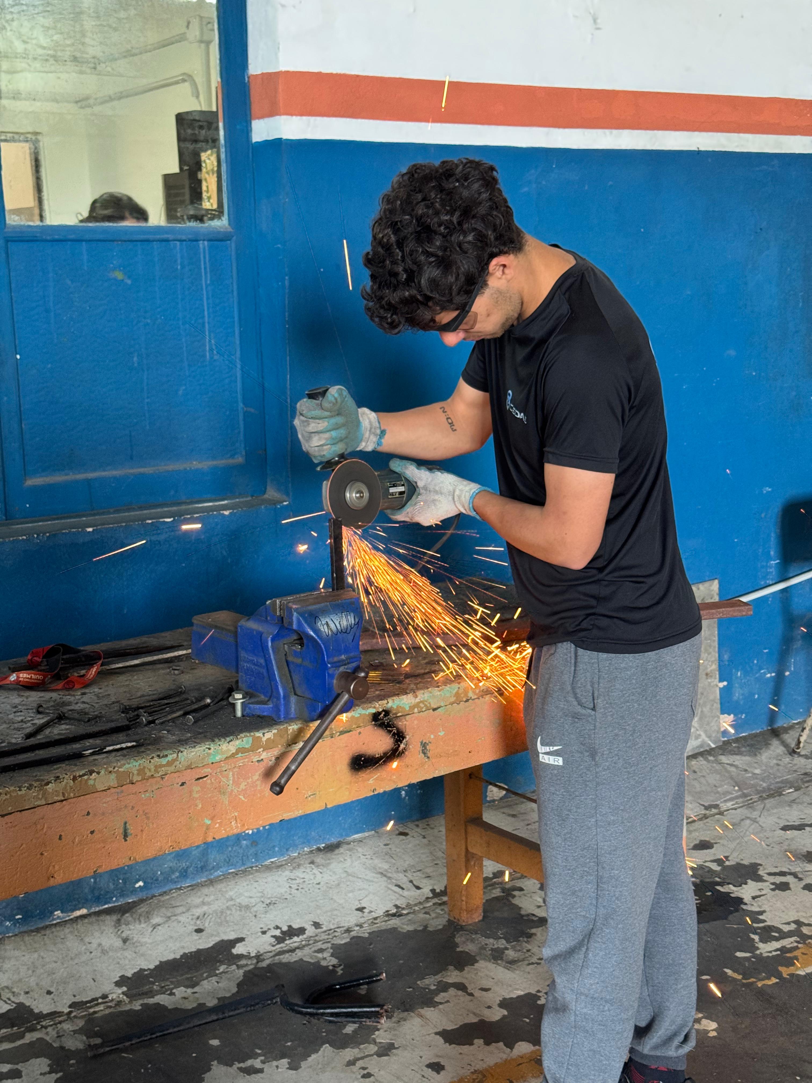
Estructura/cortando la estructura para panel.jpg
