impatrq/AVIS/Estructura/Croquis/Cabina Frontal.jpeg

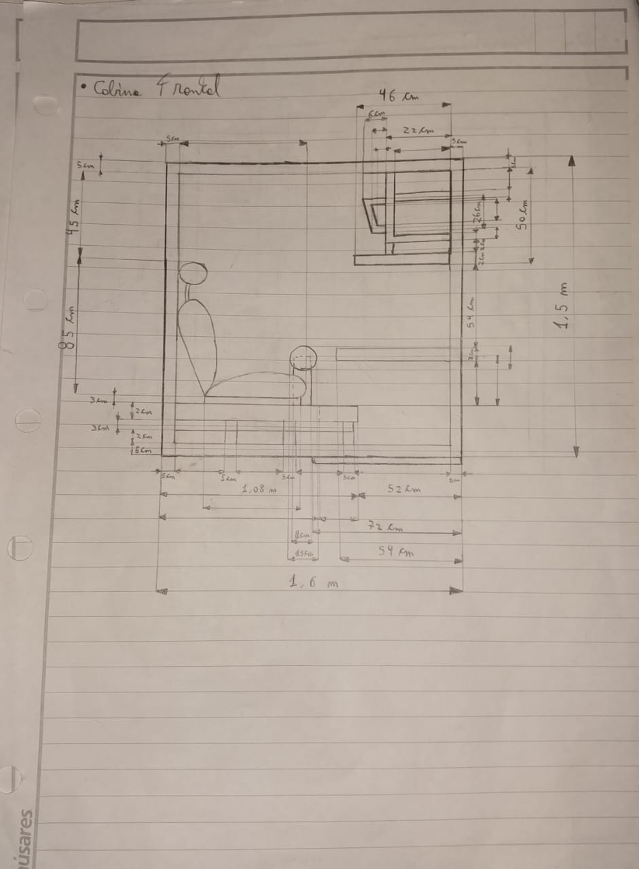
Estructura/Croquis/Cabina Frontal.jpeg
