impatrq/AVIS/Estructura/Croquis/Cabina Lateral.jpeg

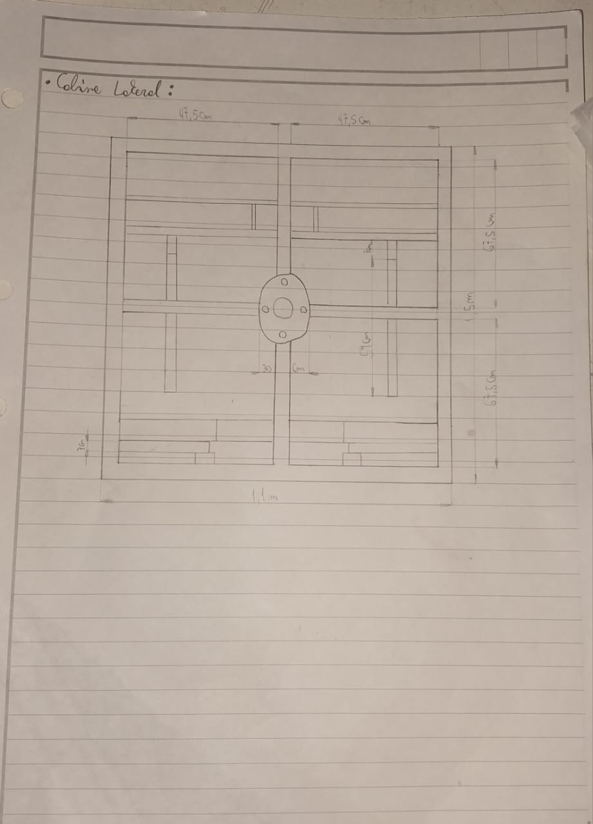
Estructura/Croquis/Cabina Lateral.jpeg
