impatrq/AVIS/Estructura/Croquis/Soporte Frontal.jpeg

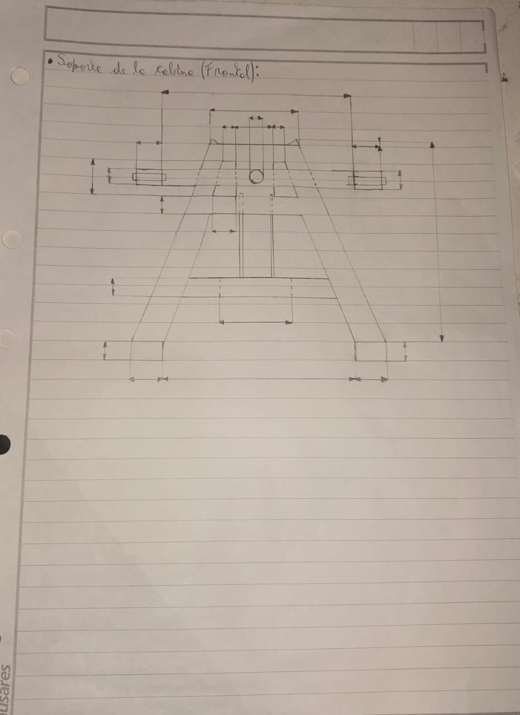
Estructura/Croquis/Soporte Frontal.jpeg
