impatrq/AVIS/Estructura/Croquis/Soporte Trasero.jpeg

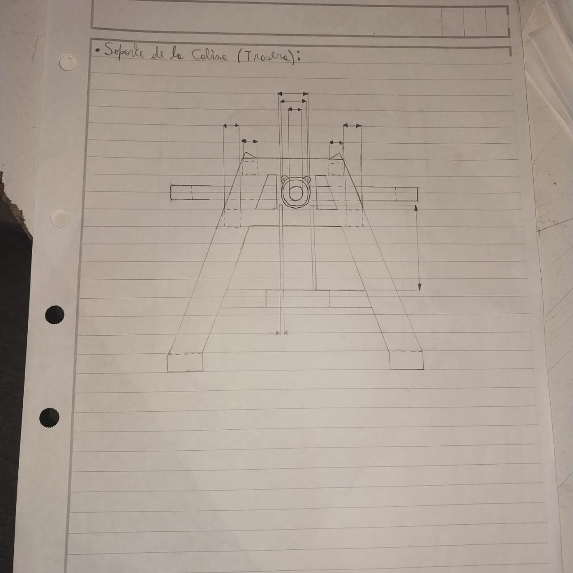
Estructura/Croquis/Soporte Trasero.jpeg
