impatrq/AVIS/Estructura/madera poterior.jpg

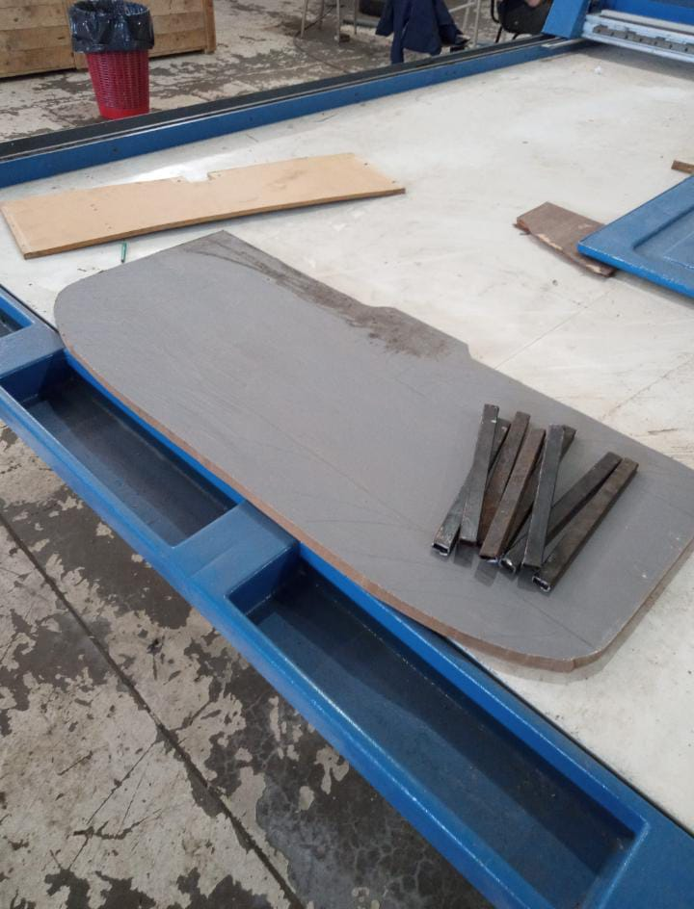
Estructura/madera poterior.jpg
