impatrq/AVIS/Estructura/medidas.jpg

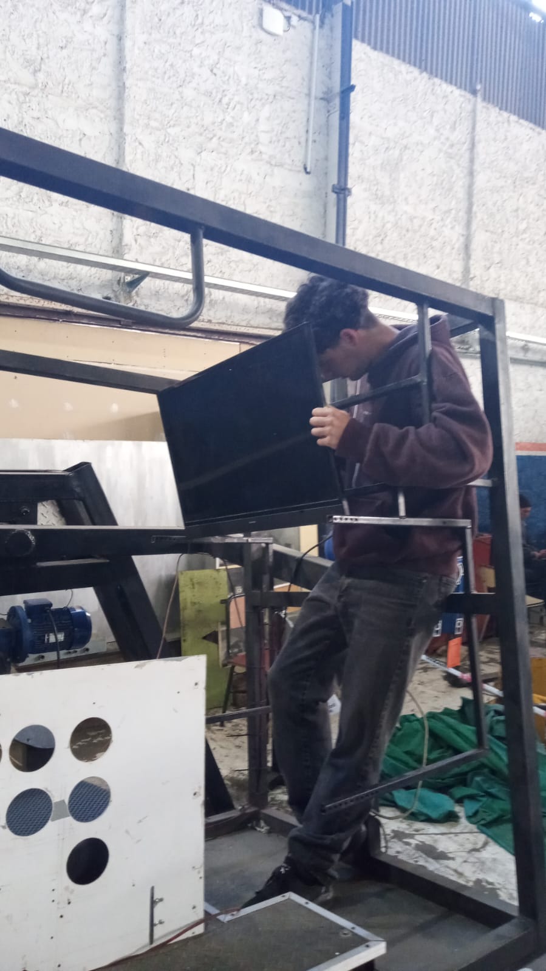
Estructura/medidas.jpg
