impatrq/AVIS/Estructura/Motores/Dimensiones Pre Cajas/Croquis.png

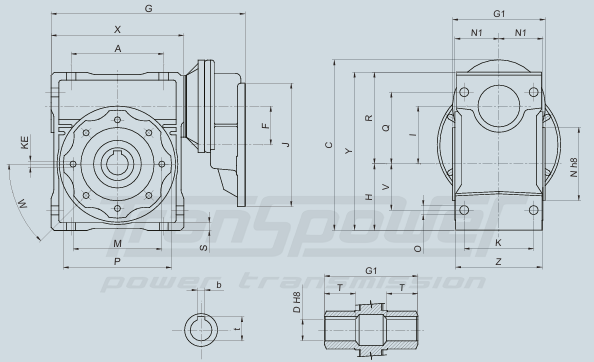
Estructura/Motores/Dimensiones Pre Cajas/Croquis.png
