impatrq/AVIS/Estructura/soldando.jpg

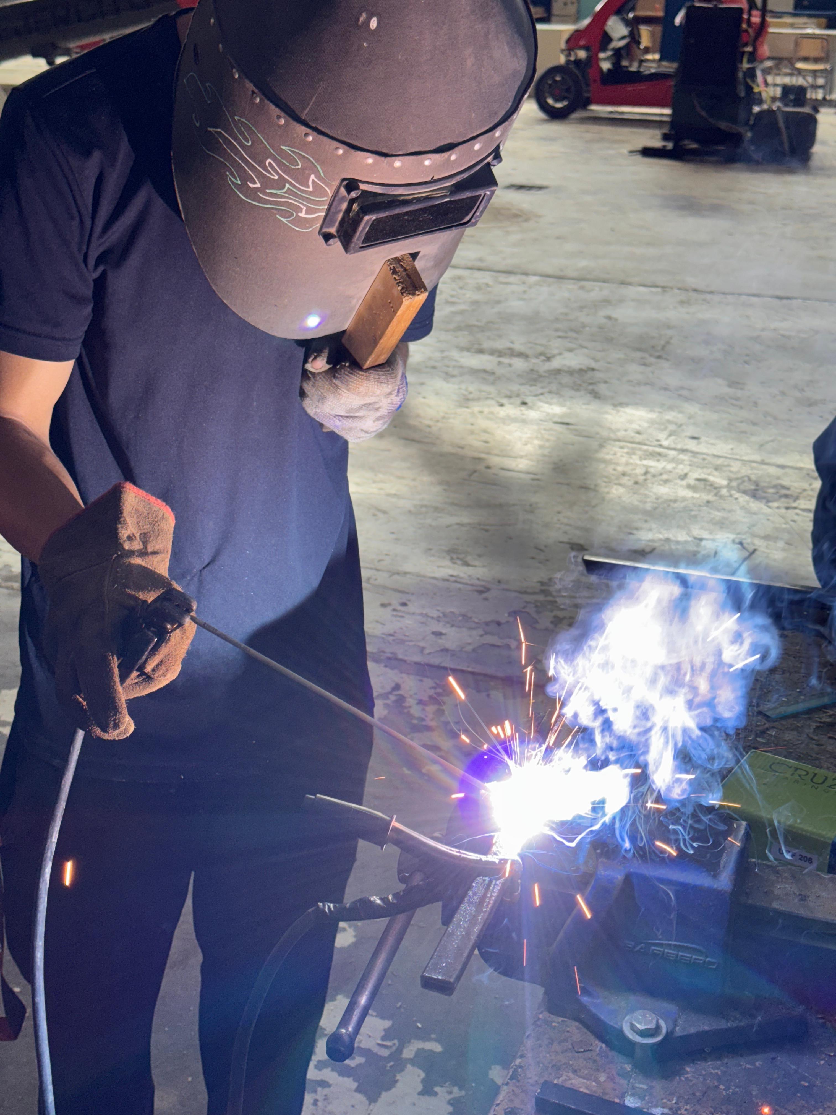
Estructura/soldando.jpg
