impatrq/AVIS/Microsoft Flight Simulator/Panel de Control/Diagramas del Panel/Panel actual/diagrama bloque cessna 152.png

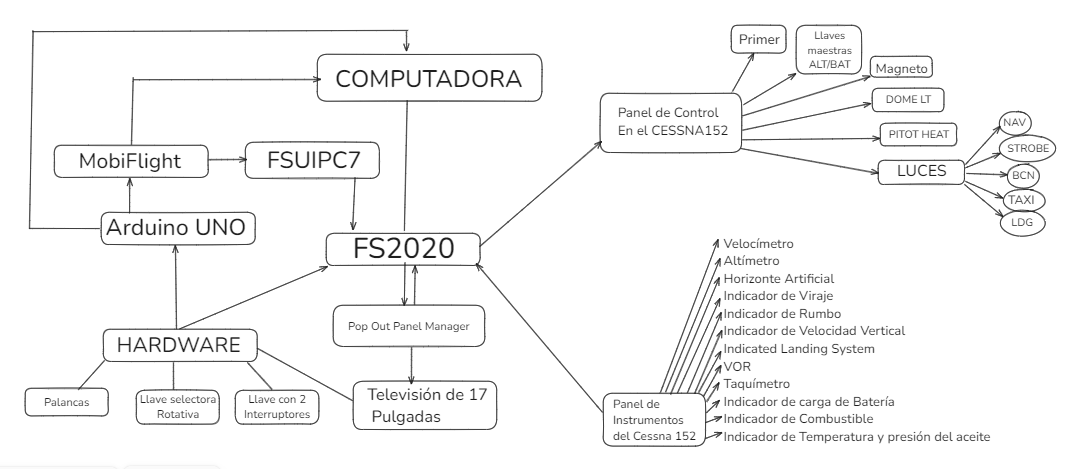
Microsoft Flight Simulator/Panel de Control/Diagramas del Panel/Panel actual/diagrama bloque cessna 152.png
