impatrq/AVIS/Microsoft Flight Simulator/Panel de Control/Modelos 3D del Panel de Control/WhatsApp Image 2024-11-27 at 17.26.18.jpeg

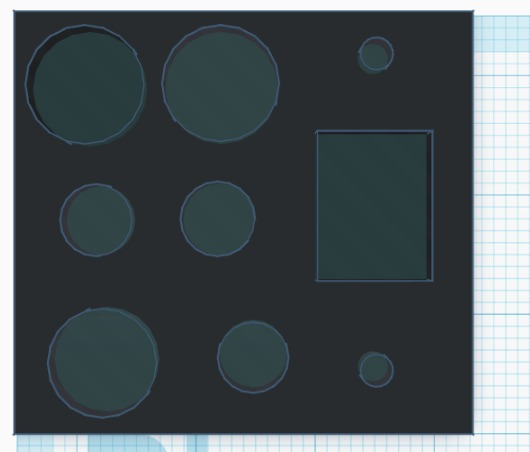
Microsoft Flight Simulator/Panel de Control/Modelos 3D del Panel de Control/WhatsApp Image 2024-11-27 at 17.26.18.jpeg
