impatrq/AVIS/Pagina web/images/esteban.jpg

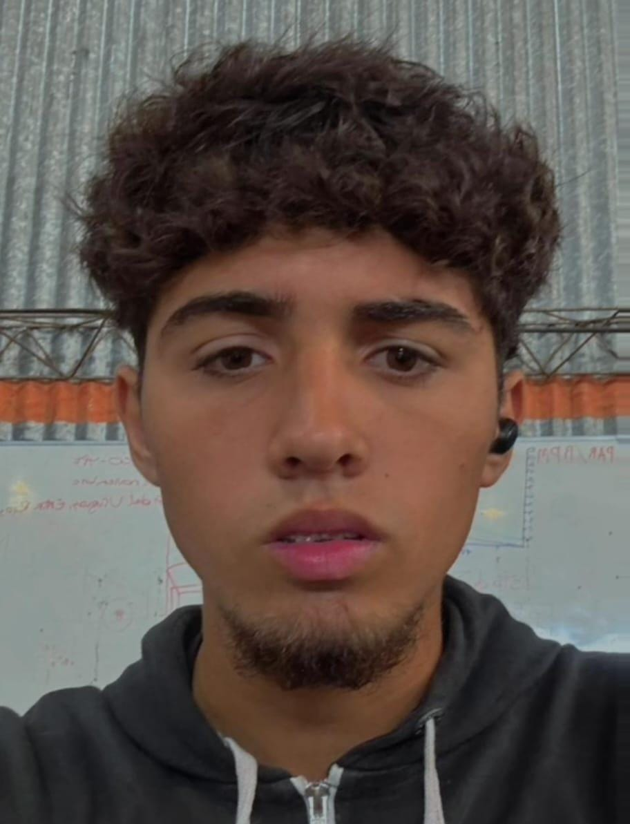
Pagina web/images/esteban.jpg
