impatrq/AVIS/Pagina web/images/estructura1.jpg

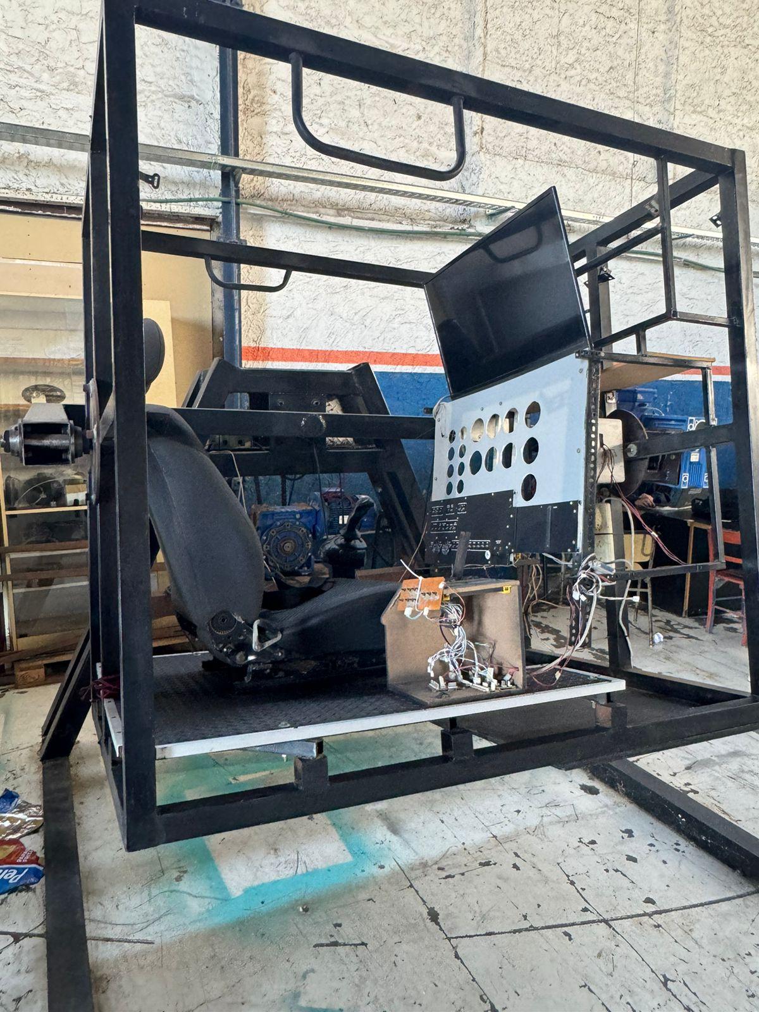
Pagina web/images/estructura1.jpg
