impatrq/AVIS/Pagina web/images/estructura3.jpg

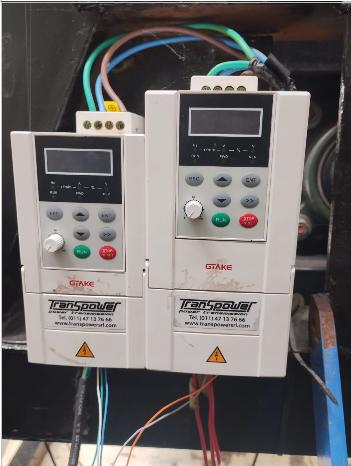
Pagina web/images/estructura3.jpg
