impatrq/AVIS/Pagina web/images/estructura4.jpg

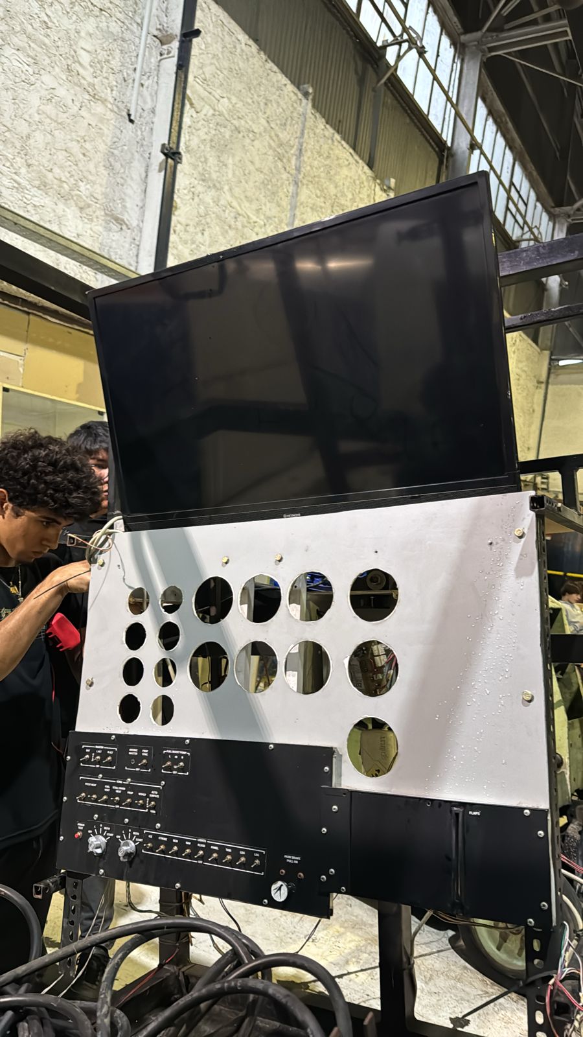
Pagina web/images/estructura4.jpg
