impatrq/AVIS/Pagina web/images/flores.jpg

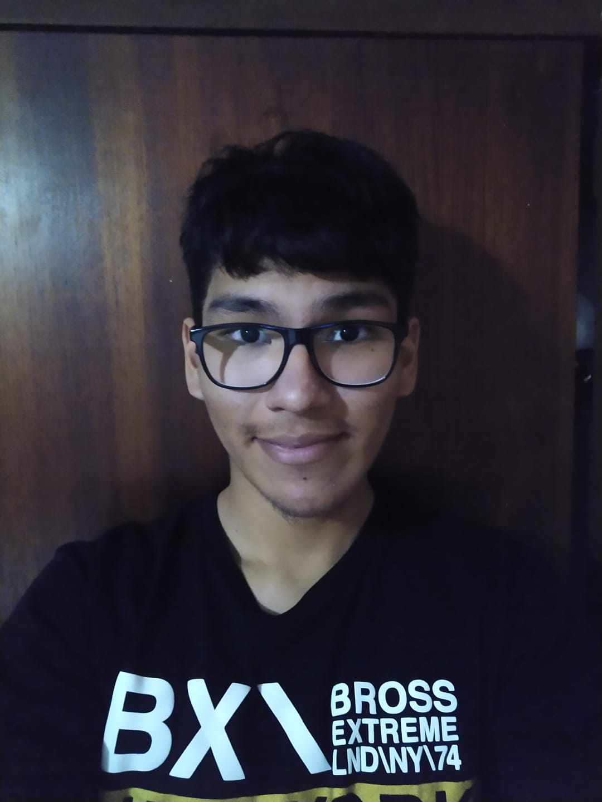
Pagina web/images/flores.jpg
