impatrq/AVIS/Pagina web/images/godoy.jpg

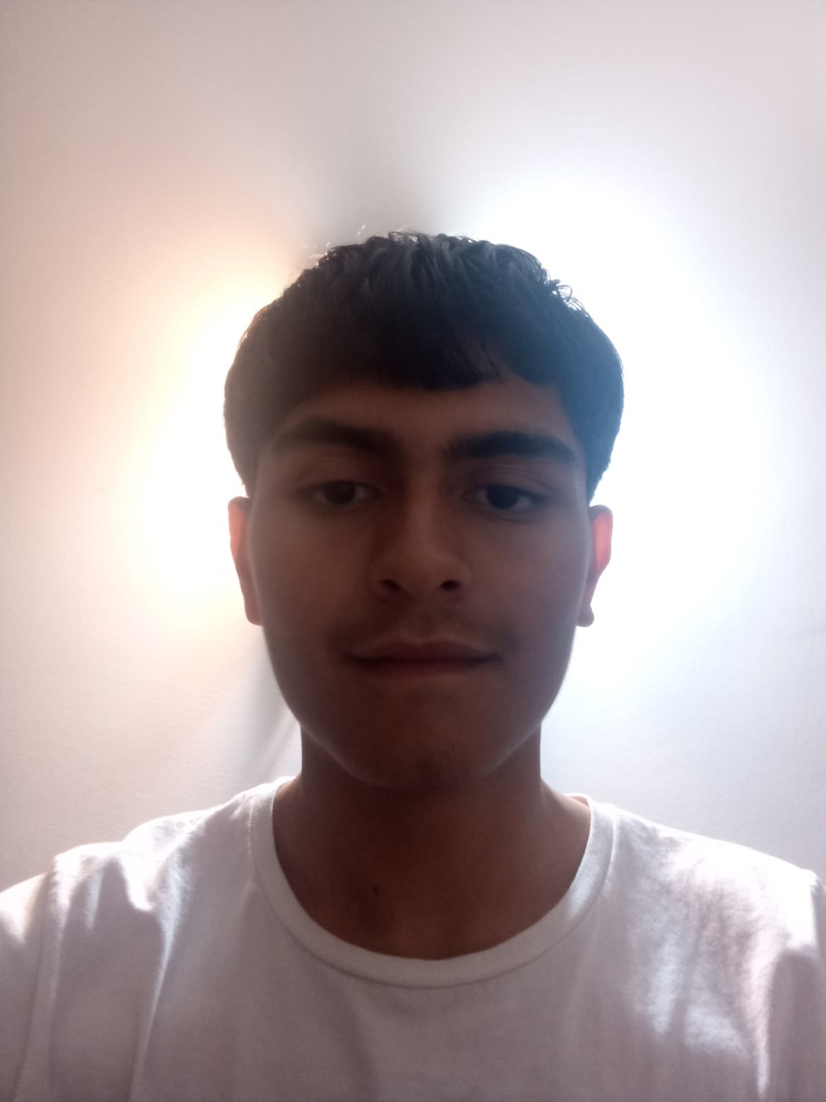
Pagina web/images/godoy.jpg
