impatrq/AVIS/Pagina web/images/leiva.jpg

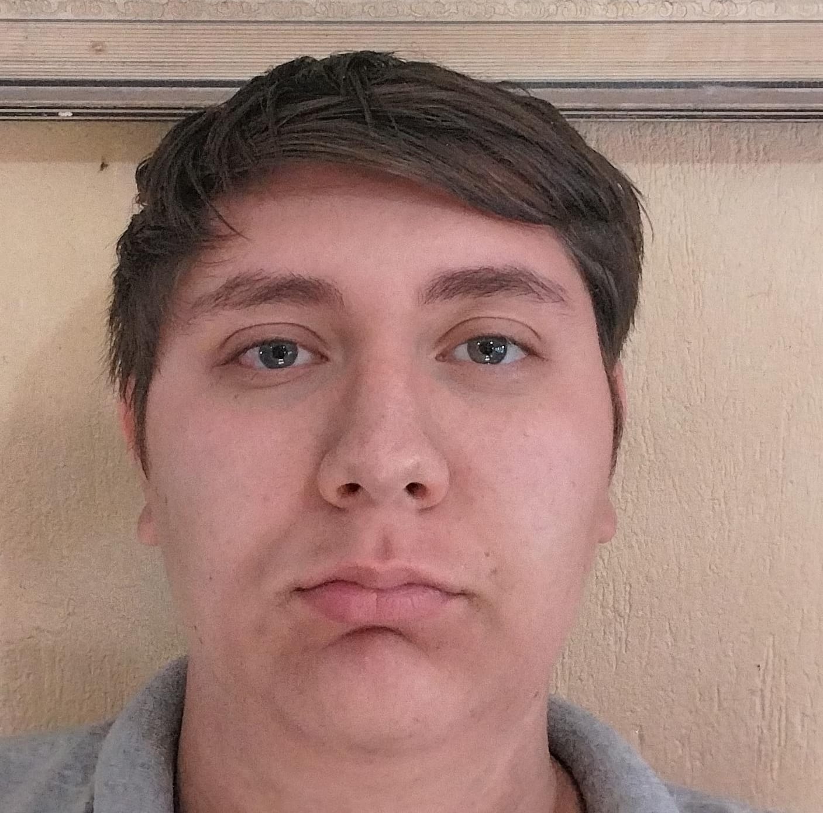
Pagina web/images/leiva.jpg
