impatrq/AVIS/Pagina web/images/rubio.jpg

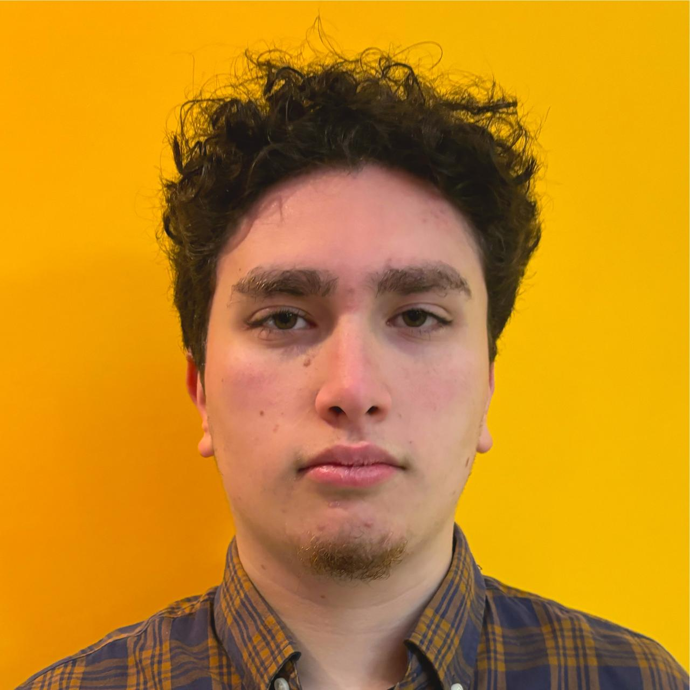
Pagina web/images/rubio.jpg
