impatrq/AVIS/Variadores de frecuencia/Placa PCB hecha en KICad/Placa PCB con sus huellas correspondientes de cada componente.png

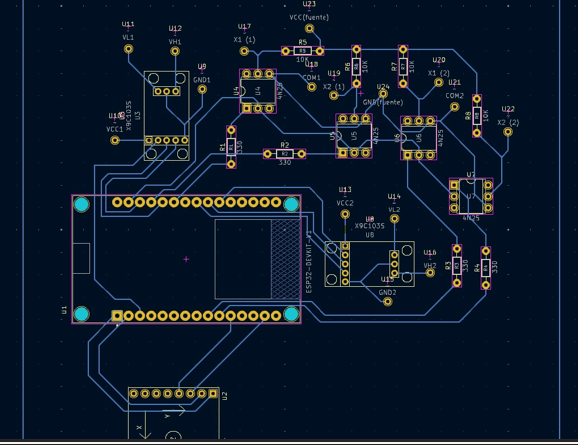
Variadores de frecuencia/Placa PCB hecha en KICad/Placa PCB con sus huellas correspondientes de cada componente.png
