impatrq/AVIS/Microsoft Flight Simulator/Panel de Control/Panel de Control Cessna 152/Rearmado del Panel de Control en cabina Cessna 152/Medidas/Medir la llave selectora rotativa MAGNETO.pdf

Medir la llave selectora rotativa (lo que va a ser el MAGNETO) para ubicarlo correctamente en el panel
Medidas
- Ancho: 23,6mm
- Alto: 27mm
