impatrq/AVIS/variadores de frecuencia/pruebas con el osciloscopio/osci.jpeg

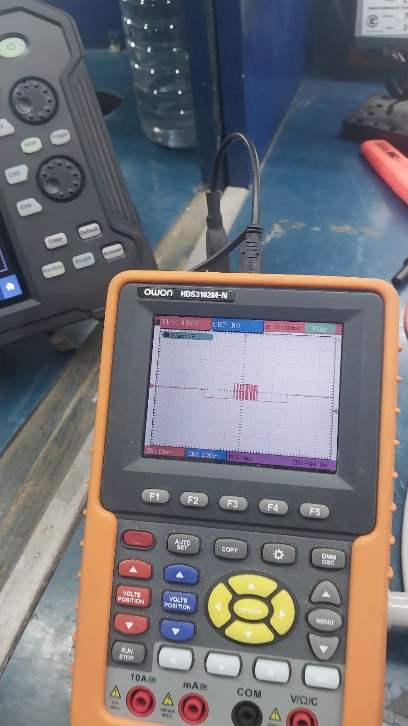
variadores de frecuencia/pruebas con el osciloscopio/osci.jpeg
